Miluino/Miluino_MA1_hardware/docs/Техническая документация/02_Питание_и_внешние_выходы.md

# Питание платы и ограничение питания внешних устройств

## Источники и домены

Плата имеет два раздельных USB-C Device/UFP/Sink и вход VIN. От USB-C DAP постоянно формируется `+3V3_DAP` для STM32F103. Локальная target получает `+5V_TGT` от одного выбранного источника: коммутируемого VBUS USB-C DAP (`+5V_DAP_USB`), VBUS USB-C target (`USB_VBUS`) либо преобразованного VIN (`+5V_IN_Line`). От `+5V_TGT` отдельный TLV76133DCYR формирует `+3V3_TGT` для К1986. Общая GND не создаёт гальванической изоляции между доменами.

```text
USB-C DAP / USB_DAP_VBUS ─┬─ TLV76133DCYR ────────── +3V3_DAP
                          ├─ TPS2553-1 ────────────── +5V_DAP_OUT
                          │                 └─ Schottky + TLV76133DCYR ─ +3V3_DAP_OUT
                          └─ P-MOSFET ─ +5V_DAP_USB ───────┐
USB-C target / USB_VBUS ────────────────────────────────────┼─ T-селектор ─ +5V_TGT ─┬─ TLV76133DCYR ─ +3V3_TGT
VIN 8...18 В ─ LMR51410XDBVR ─ +5V_IN_Line ────────────────┘                        └─ TPS2553-1 ─ +5V_Out_Line
                                                                                                      └─ Schottky + TLV76133DCYR ─ +3V3_Out_Line
```

`+5V_Out_Line` и `+3V3_Out_Line` — имена защищённых электрических сетей ветви Output Power. Питание внешних устройств через Arduino и соответствующие контакты STMorpho берётся именно с этих сетей. `+5V_DAP_OUT` и `+3V3_DAP_OUT` образуют отдельную ветвь внешнего питания от USB-C DAP.

## Выбор питания локальной target

T-образный четырёхконтактный селектор имеет центральный контакт `+5V_TGT` и три внешних контакта источников. Один джампер соединяет только один источник с target; автоматического приоритета нет. Одновременно подключённые физические источники допустимы, поскольку невыбранные входы селектора разомкнуты. Без джампера силовое питание target отключено, тогда как домен DAP может оставаться под напряжением.

| Вход селектора | Путь | Особенность |
|---|---|---|
| DAP | `USB_DAP_VBUS` → P-MOSFET → `+5V_DAP_USB` | Ключ управляется STM32F103; ток target обходит TPS2553-1 внешних выходов DAP. |
| USB target | `USB_VBUS` USB-C target напрямую | Дополнительного eFuse либо ограничения тока VBUS на плате нет. |
| VIN | VIN → LMR51410XDBVR → `+5V_IN_Line` | Вход 8...18 В, номинально 12 В; защита от переполюсовки и длительного перенапряжения требуется от внешнего источника. |

VIN на Arduino и STMorpho относится к одной входной сети. Контакты +5V/+3V3 Arduino, выходы DAP и прямые контакты STMorpho не служат входами питания платы. BUcc К1986 соединён с `+3V3_TGT`; отдельного резервного источника нет.

### Преобразователь VIN

Выбран LMR51410XDBVR: синхронный понижающий преобразователь 400 кГц, PFM при малой нагрузке, номинальный ток микросхемы 1 А. В схеме предусмотрены входные 4,7 мкФ и 100 нФ X7R на 50 В, дроссель 33 мкГн с `Irms ≥ 1,5 А` и `Isat ≥ 2,5 А`, bootstrap 100 нФ X7R на 16 В, выходные 22 мкФ X7R на 16 В и делитель FB 118 кОм / 22,1 кОм с допуском 1 %. EN подключён непосредственно к VIN; отдельный UVLO-делитель не установлен. Встроенная аварийная защита преобразователя не задаёт допустимый ток внешней нагрузки.

### Стабилизаторы 3,3 В

Четыре ветви используют TLV76133DCYR: `+3V3_DAP`, `+3V3_TGT`, `+3V3_DAP_OUT` и `+3V3_Out_Line`. Для каждого LDO предусмотрены керамические X7R: 1 мкФ на входе и 4,7 мкФ на выходе; эффективную выходную ёмкость и тепловой режим необходимо подтвердить для выбранных компонентов и разводки. Внешние ветви 3,3 В питаются через отдельные последовательные диоды Шоттки. В схеме для DAP это VD101/VD102, для Output Power — VD1/VD2: первый диод каждой пары блокирует продолжительное обратное питание пятивольтового выхода, второй соединяет выход LDO с его входом в направлении отвода обратного тока. Конкретные диоды ещё не выбраны; эта схема не является идеальной безынерционной развязкой источников.

## Два независимых ограничителя тока

| Ветвь | Вход и выходы | Управление | Установка ограничения |
|---|---|---|---|
| Внешние выходы DAP | `USB_DAP_VBUS` → TPS2553-1 → `+5V_DAP_OUT` и LDO `+3V3_DAP_OUT` | `DAP_TARGET_PWR_EN` от PA1 STM32F103 | R122 = 100 кОм, 1 % |
| Output Power | `+5V_TGT` → TPS2553-1 → `+5V_Out_Line` и LDO `+3V3_Out_Line` | `TGT_OUTPUT_PWR_EN` от PB10 К1986 | R28 = 100 кОм, 1 % |

Каждый TPS2553-1 ограничивает общий входной ток **своей** пятивольтовой и трёхвольтовой нагрузок. Ток LDO 3,3 В берётся из той же защищённой ветви 5 В. При RILIM = 100 кОм типовой порог около 266 мА; расчётный разброс по формулам производителя с допуском резистора составляет ориентировочно 232...306 мА. Значение 300 мА не является гарантированным точным порогом отдельного ключа и не обеспечивается как суммарный аппаратный предел двух ключей. Диапазон и нагрев требуют измерений на прототипе.

У каждого ключа предусмотрены входной X7R 1 мкФ и выходной X7R 22 мкФ; эффективная выходная ёмкость при рабочем напряжении должна быть не менее 10 мкФ. Выходы двух ключей между собой не объединяются. Версия `-1` защёлкивает аварийное отключение: для восстановления требуется переключить соответствующий EN либо снять питание; автоматическое программное повторное включение не предусмотрено.

### Внешние выходы DAP

`+5V_DAP_OUT` и `+3V3_DAP_OUT` расположены отдельно от XP7 и имеют общий ограничитель тока. GND внешней платы берётся с соседнего `SPARE JMP`. Контакт XP7.1 `EXT_VTREF` остаётся входом фактического питания логики внешней target: 3,3 В необходимо вернуть на него даже при питании платы от одного из выходов DAP. При использовании выхода 5 В внешняя плата должна самостоятельно сформировать 3,3 В для своей логики.

PA1 STM32F103 формирует активный высоким уровнем `DAP_TARGET_PWR_EN`: он напрямую подан на EN первого TPS2553-1 и через R112 = 1 кОм управляет затвором NMOS 2N7002 в цепи силового P-MOSFET. Подтяжка затвора NMOS к GND 10 кОм и подтяжка затвора P-MOSFET к его истоку удерживают оба тракта выключенными после сброса. Прошивка разрешает их после USB `SET_CONFIGURATION` для конфигурации 500 мА и отключает при suspend, сбросе или деконфигурации USB и потере VBUS. `FAULT` этого TPS2553-1 подключён только к местной цепи светодиода, к микроконтроллерам он не подаётся.

TPS2553-1 имеет защиту от обратного напряжения с конечным временем отключения. Она блокирует продолжительную подпитку VBUS через внешний выход, но не заменяет мгновенный ideal-diode. Подавать на выходы питание от другого источника без специально рассчитанной развязки нельзя. Для 3,3-вольтового LDO возможны кратковременный заряд его входной ёмкости и токи утечки; допустимость конкретной внешней схемы подтверждается измерениями.

### Output Power для Arduino и STMorpho

PB10 К1986 (вывод 55) через штатно установленный R1004 = 0 Ом управляет сетью `TGT_OUTPUT_PWR_EN` и EN второго TPS2553-1 независимо от выбранного входа T-селектора. R27 = 10 кОм подтягивает EN к GND: при сбросе и до настройки PB10 выходы выключены. Включение выполняется только по явной команде прошивки. Альтернативный R1104 = 0 Ом к `PB10_Line`/CN10.2 штатно не установлен; одновременная установка R1004 и R1104 запрещена. `DAP_TARGET_PWR_EN` электрически не управляет этим ключом.

| Шина | Контакты Arduino | Защищённые контакты STMorpho |
|---|---|---|
| `+5V_Out_Line` | +5V | CN7.11, CN7.18 |
| `+3V3_Out_Line` | +3V3 | CN7.9, CN7.16 |

Нагрузки всех перечисленных контактов суммируются на входе второго TPS2553-1. Выходы разрешены только как источники питания внешних устройств; обратная подача напряжения запрещена. Номиналы светодиодов и их последовательных резисторов в цепях `FAULT` обеих ветвей пока не выбраны.

### Прямые контакты STMorpho для контроля питания

| Сеть | Контакты | Допустимое применение |
|---|---|---|
| `+3V3_TGT` | CN7.5, CN7.12 (IOREF), CN7.33 (BUcc) | Только высокоомное измерение напряжения. |
| `+5V_TGT` | CN7.6, CN7.26, CN10.8 | Только высокоомное измерение напряжения. |

Эти контакты находятся **до** второго TPS2553-1. Питать от них shield или иную внешнюю нагрузку и подавать на них напряжение нельзя: ключ не ограничит такой ток и не защитит от обратной подачи. IOREF показывает питание логики К1986 даже при выключенной ветви Output Power; CN7.26 позволяет контролировать `+5V_TGT` при её выключении.

## Индикация и контроль аварии

`FAULT` ключа Output Power имеет активный низкий уровень, подтянут R26 = 100 кОм к `+5V_TGT` и подключён к локальному индикатору. Этот же узел соединён с затвором VT1 = 2N7002; исток VT1 соединён с GND, сток подтянут R24 = 10 кОм к `+3V3_TGT`. Штатно не установленный R25 = 1 кОм может соединить сток с PE3 К1986 и STMorpho CN10.10. При установленном R25 **высокий уровень PE3 означает аварию**, низкий — отсутствие активного `FAULT`, но не доказывает наличие выходного напряжения. В такой комплектации CN10.10 нельзя независимо использовать шилдом. В базовой комплектации R25 = DNP и PE3 остаётся GPIO.

`FAULT` ключа внешних выходов DAP остаётся только на местном светодиоде; STM32F103 и К1986 его не считывают. Цвет, модели и токоограничивающие резисторы обоих индикаторов ожидают выбора конкретных светодиодов.

## Бюджет USB-C DAP и других источников

Для работы от USB-C DAP принят бюджет 500 мА: до 100 мА с запасом на STM32F103, до 100 мА с запасом на К1986 и **не более 300 мА суммарно** на все внешние нагрузки двух ветвей (`+5V_DAP_OUT`/`+3V3_DAP_OUT` и Output Power на Arduino/STMorpho). Это эксплуатационный бюджет, а не общий порог двух TPS2553-1. Ток нештатной нагрузки прямых контактов STMorpho также потреблял бы этот бюджет, не проходя через Output Power TPS2553-1.

При питании target от USB-C target потребление должно соответствовать разрешённому его USB-хостом току; конфигурация USB-C DAP на этот порт не распространяется. Для VIN допустимый ток определяют внешний источник, преобразователь, тепловой режим и проверка прототипа. Номинальный ток LMR51410XDBVR 1 А не является разрешением нагружать разъёмы платы на 1 А.

## USB-C и защита портов

Оба USB-C работают только как Device/UFP/Sink: CC1 и CC2 каждого разъёма имеют отдельные Rd 5,1 кОм, 1 % к GND. Высокие напряжения USB Power Delivery, Host/Source и обратная подача на VBUS не поддерживаются. Пары A6/B6 и A7/B7 розетки объединяются соответственно как D+ и D−. Экраны обоих разъёмов соединяются с GND напрямую.

На D+/D− каждого порта установлена отдельная малоёмкостная сборка USBLC6-2SC6 по проходной схеме; её VBUS подключён к VBUS соответствующего разъёма, GND — коротким соединением к общей земле. Рядом находятся локальные конденсаторы VBUS 100 нФ: C110 у DAP и C6 у target. Они развязывают VBUS и не меняют роль USBLC6-2SC6: сборка защищает сигнальные линии от ESD, но не ограничивает силовой ток. Последовательные резисторы USB D+/D− и CC-подтяжки остаются самостоятельными элементами.

## Сброс, полное отключение и ограничения

При изменении MODE К1986 требуется полный power cycle. Снятие джампера T-селектора разрывает штатные силовые пути target, но включённый DAP или внешний shield может частично подпитывать выключенный домен через сигнальные линии SWD/JTAG, VCP, MCO, USB или GPIO. Перед отключением target необходимо исключить активные сигналы в выключенный домен; для DAP доступны `DAP_ROUTE=OFF`, отключение VCP и снятие R1003 линии MCO. Постоянный разрядный резистор `+3V3_TGT` установлен, его окончательный номинал и время разряда проверяются на прототипе. Индикатор питания target не заменяет измерение остаточного напряжения.

Открыты для проверки на прототипе: фактические пороги двух TPS2553-1, ёмкости конденсаторов при рабочем смещении, нагрев LDO и преобразователя, обратные токи через выходы, время разряда `+3V3_TGT`, работа при одновременном подключении двух USB-хостов и конкретные типы диодов, MOSFET и индикаторов.

См. также [общее описание](01_Общее_описание_платы.md), [распиновку К1986](03_К1986_распиновка_и_программирование.md) и [распиновку DAP](04_Программатор_распиновка.md).
