Miluino/Miluino_MA1_hardware/docs/Техническая документация/03_К1986_распиновка_и_программирование.md

# К1986ВЕ92FI: распиновка, переключатели и программирование

## Электрические условия

К1986ВЕ92FI питается от `+3V3_TGT`, сформированной из выбранной T-селектором шины `+5V_TGT`. BUcc подключён к тому же домену; независимого резервного питания нет. Логические уровни Arduino, STMorpho и интерфейсов отладки рассчитаны на 3,3 В. Силовые контакты +5V/+3V3 Arduino получают питание от включаемой отдельно ветви Output Power; IOREF всегда показывает `+3V3_TGT`. Контакты Morpho, соединённые с `+5V_TGT` и `+3V3_TGT` напрямую, предназначены только для высокоомного контроля напряжения: перечень и ограничения приведены в [документе по питанию](02_Питание_и_внешние_выходы.md).

## Все выводы К1986ВЕ92FI

В таблице указан физический номер вывода корпуса и его связь с разъёмами при штатной комплектации. Для переключаемых цепей приведены оба функциональных варианта; DNP-ветвь проводит сигнал только после установки соответствующего резистора.

| № | Вывод К1986 | Arduino | STMorpho / внешний узел | Назначение |
|---:|---|---|---|---|
| 1 | Ucc | IOREF показывает эту шину; контакт Arduino +3V3 питается отдельно | Шина `+3V3_TGT`; CN7.5/CN7.12 | Основное цифровое питание, обязательна локальная развязка |
| 2 | PF0 | D11/MOSI через `SEL_D11_SPI_PWM` | CN7.1 RAW; CN10.15 через D11_SEL | SSP1_TXD; в MODE=110 используется UART2-загрузчиком |
| 3 | PF1 | D13/SCK | CN10.11 | SSP1_CLK; локальный LED не подключается; в MODE=110 используется UART2-загрузчиком |
| 4 | PF2 | D10/CS через `SEL_D10_SPI_PWM` | CN10.18 RAW; CN10.17 через D10_SEL | SSP1_FSS; не объединять напрямую с PA2 |
| 5 | PF3 | D12/MISO | CN10.13 | SSP1_RXD, прямое соединение |
| 6 | PF4/MODE0 | - | Только локальный конфигуратор MODE0 | Бит MODE0; намеренно не соединяется с CN7.7/BOOT0, Morpho и внешними разъёмами |
| 7 | PF5/MODE1 | - | Только локальный конфигуратор MODE1 | Бит MODE1; намеренно не выводится на Morpho и внешние разъёмы |
| 8 | PF6/MODE2 | - | Только локальный конфигуратор MODE2 | Бит MODE2; намеренно не выводится на Morpho и внешние разъёмы |
| 9 | DP | - | CN10.12; USB-C целевого МК | USB D+; позиция соответствует PA12/USB_DP NUCLEO-F103RB; не объединять с USB встроенного отладчика |
| 10 | DN | - | CN10.14; USB-C целевого МК | USB D-; позиция соответствует PA11/USB_DM NUCLEO-F103RB; требуется ESD-защита и обвязка по datasheet |
| 11 | GND | GND | Общая GND; контакты GND Morpho | Цифровая земля |
| 12 | Ucc | IOREF показывает эту шину; контакт Arduino +3V3 питается отдельно | Шина `+3V3_TGT`; CN7.5/CN7.12 | Основное цифровое питание, обязательна локальная развязка |
| 13 | BUcc | — | CN7.33 | BUcc напрямую питается от основной целевой шины `+3V3_TGT`; отдельный резервный источник не предусмотрен. CN7.33 допускается только для высокоомного контроля напряжения, без питания шилда и внешней подачи напряжения |
| 14 | STANDBY | - | CN7.4 через R11 (`R_STANDBY_SER`) | Выходной флаг режима Standby; без подтяжки, shield использует линию только как вход |
| 15 | PE7/OSC32_OUT | - | CN7.27 | LSE-кварц либо GPIO через взаимоисключающие мосты; позиция соответствует PC15/OSC32_OUT F103RB |
| 16 | PE6/OSC32_IN | - | CN7.25 | LSE-кварц либо GPIO через взаимоисключающие мосты; позиция соответствует PC14/OSC32_IN F103RB |
| 17 | WAKEUP | - | CN7.3 через нормально не установленный `R_WAKEUP_EN`; R12 (`R_WAKEUP_PULL`) к VCC установлен, номинал уточняется | Активный низким уровнем вход пробуждения из Standby; внешний источник только open-drain/open-collector, 3,3 В |
| 18 | RESET | RESET | CN7.14 | `TARGET_nRESET` с единственной подтяжкой к `+3V3_TGT` и C1=100 нФ к GND; все внешние источники только open-drain/open-collector |
| 19 | OSC_IN | - | DAP_MCO через R109 и R1003 default; X_HSE через R1103; CN7.29 через R1203 | Штатный вход 8 МГц от DAP; для MCO/внешнего генератора требуется HSEBYP=1, для локального кварца HSEBYP=0 |
| 20 | OSC_OUT | - | X_HSE через R1213; CN7.31 через R1113; к DAP не подключать | Выход аналогового усилителя HSE в режиме кварца; в режиме DAP_MCO должен оставаться ненагруженным |
| 21 | PE3 | - | CN10.10; сток VT1 через штатно не установленный R25=1 кОм | Свободный GPIO при DNP R25; после установки R25 — вход аварии ветви Output Power, высокий уровень означает срабатывание `FAULT`; shield не должен управлять CN10.10 |
| 22 | PE2 | D3/PWM | CN10.31 | TMR2_CH3; аппаратный PWM |
| 23 | AGND1 | - | Общая аналоговая земля; CN10.32 | Отдельный физический вывод, на Morpho доступен через общую сеть AGND |
| 24 | AUcc1 | - | Общая аналоговая шина; на CN10.7 не выведена | Отдельный физический вывод аналогового питания; CN10.7 подключён к `AREF_Line` |
| 25 | PE1 | - | CN7.37 | Свободный GPIO; также DAC2_REF и альтернативные CAN/таймерные функции |
| 26 | PE0/DAC2_OUT | A0 в положении DAC `SEL_A0_ADC_DAC` | CN10.6 RAW; CN7.28 через A0_SEL | Выход ЦАП; нельзя объединять напрямую с PD2 |
| 27 | AGND | - | CN10.32 | Основная аналоговая земля; постоянно соединяется с общей GND с учётом требований к разводке |
| 28 | AUcc | — | - | Аналоговое питание и внутренняя опора АЦП; на CN10.7 выведена отдельная сеть `AREF_Line`, штатно связанная с `+3V3_TGT` через R1009 |
| 29 | PD7/ADC7 | A5 в положении ADC | CN10.28 RAW; CN7.38 через A5_SEL | Освобождается, если A5 переключён на I2C/SCL |
| 30 | PD4/ADC4/JB_TDO | A2 | CN7.32 | Недоступен как ADC во время отладки через JTAG_B |
| 31 | PD0/ADC0_REF+/UART2_RXD/JB_TMS | - | CN10.34/JTAG_B через R1005; DAP_VCP_TX через R1105; R1109 соединяет AREF с `PD0/JB_TMS_Line` и штатно не установлен | Будущая внешняя опора: R1109+R1005 установлены, CN10.34 не используется, JTAG_B отключён |
| 32 | PD1/ADC1_REF-/UART2_TXD/JB_TCK | - | CN10.36/JTAG_B через R1006; DAP_VCP_RX через R1106; R1206=0 Ом (DNP) к GND со стороны МК | Для будущей внешней опоры R1006/R1106 сняты, R1206 установлен; штатно доступен RAW/VCP по установленному каналу |
| 33 | PD2/ADC2/JB_TRST | A0 в положении ADC `SEL_A0_ADC_DAC` | CN10.4 RAW; CN7.28 через A0_SEL | Штатный аналоговый вход A0; конфликт с JTAG_B |
| 34 | PD3/ADC3/JB_TDI | A1 | CN7.30 | Прямой аналоговый вход; конфликт с JTAG_B |
| 35 | PD5/ADC5 | A3 | CN7.34 | Прямой аналоговый вход; JTAG_B его не занимает |
| 36 | PD6/ADC6 | A4 в положении ADC | CN10.26 RAW; CN7.36 через A4_SEL | Освобождается, если A4 переключён на I2C/SDA |
| 37 | NC | - | Не подключать | Корпусной вывод без электрического подключения |
| 38 | Ucc | IOREF показывает эту шину; контакт Arduino +3V3 питается отдельно | Шина `+3V3_TGT`; CN7.5/CN7.12 | Основное цифровое питание, обязательна локальная развязка |
| 39 | GND | GND | Общая GND; контакты GND Morpho | Цифровая земля |
| 40 | PC2 | - | CN7.35 | Свободный GPIO |
| 41 | PC1/SDA1 | D18/SDA; A4 в положении I2C | CN10.5; CN10.38 RAW; CN7.36 через A4_SEL | В режиме I2C A4 и D18 являются одной сетью SDA |
| 42 | PC0/SCL1 | D19/SCL; A5 в положении I2C | CN10.3; CN10.30 RAW; CN7.38 через A5_SEL | В режиме I2C A5 и D19 являются одной сетью SCL |
| 43 | PB0/JA_TDO | - | CN7.21 | JTAG_A TDO; у F103RB совмещён с D3 на CN10.31, но здесь выведен отдельно |
| 44 | PB1/JA_TMS | - | CN7.13 | JTAG_A TMS; GPIO доступен только после отключения JTAG_A |
| 45 | PB2/JA_TCK | - | CN7.15 | JTAG_A TCK; GPIO доступен только после отключения JTAG_A |
| 46 | PB3/JA_TDI | - | CN7.17 | JTAG_A TDI; позиция соответствует PA15/JTDI NUCLEO-F103RB |
| 47 | PB4/JA_TRST | - | CN7.23 | JTAG_A TRST; у F103RB совмещён с D5 на CN10.27, но здесь выведен отдельно |
| 48 | Ucc | IOREF показывает эту шину; контакт Arduino +3V3 питается отдельно | Шина `+3V3_TGT`; CN7.5/CN7.12 | Основное цифровое питание, обязательна локальная развязка |
| 49 | GND | GND | Общая GND; контакты GND Morpho | Цифровая земля |
| 50 | PB5/UART1_TXD | D1/TX | CN10.35 | Постоянное соединение с Arduino D1; VCP использует UART2 на PD0/PD1 |
| 51 | PB6/UART1_RXD | D0/RX | CN10.37 | Постоянное соединение с Arduino D0; VCP использует UART2 на PD0/PD1 |
| 52 | PB7 | D8 | CN10.21 | Прямое соединение; свободны альтернативные таймерные функции |
| 53 | PB8 | D7 | CN10.23 | Прямое соединение; также TMR3_CH4N/COMP_OUT |
| 54 | PB9 | USER_BUTTON через `R_BUTTON_EN` | CN10.1 | GPIO/EXT_INT4; снятие `R_BUTTON_EN` отключает кнопку и её подтяжку от линии |
| 55 | PB10 | - | `TGT_OUTPUT_PWR_EN` через штатный R1004=0 Ом; CN10.2 через неустановленный R1104=0 Ом | Управление `EN` второго TPS2553-1; R27=10 кОм к GND удерживает выходы выключенными до явной команды прошивки, автоматического включения после инициализации нет |
| 56 | PA7/CAN1_RX | D5 в положении CAN | CN10.24 RAW; CN10.27 через D5_SEL | Не объединять напрямую с PA5; используется для совместимости CAN UNO R4 |
| 57 | PA6/CAN1_TX | D4/CANTX | CN10.29 | GPIO и CAN1_TX выбираются внутренним мультиплексором МК |
| 58 | PA5/TMR1_CH3 | D5 в положении PWM; LED4 через R18 (`R_LED4`) | CN10.22 RAW; CN10.27 через D5_SEL | Аппаратный PWM; установленный LED нагружает D5 при использовании линии как вход |
| 59 | PA4/TMR1_CH2N | D6/PWM | CN10.25 | Прямое соединение; аппаратный PWM |
| 60 | PA3/TMR1_CH2 | D9/PWM; LED3 через R17 (`R_LED3`) | CN10.19 | Аппаратный PWM; установленный LED нагружает D9 при использовании линии как вход |
| 61 | PA2/TMR1_CH1N | D10 в положении PWM; LED2 через R16 (`R_LED2`) | CN10.16 RAW; CN10.17 через D10_SEL | Альтернатива PF2/CS; LED не нагружает D10 в штатном SPI-положении селектора |
| 62 | PA1/TMR1_CH1 | D11 в положении PWM; LED1 через R15 (`R_LED1`) | CN7.2 RAW; CN10.15 через D11_SEL | Альтернатива PF0/MOSI; LED не нагружает D11 в штатном SPI-положении селектора |
| 63 | PA0/EXT_INT1 | D2 | CN10.33 | Прямое соединение; пользовательская кнопка перенесена на PB9 и не нагружает D2 |
| 64 | GND | GND | Общая GND; контакты GND Morpho | Цифровая земля |

## Контакты Arduino

| Контакт | Подключение к К1986 и штатная функция | Альтернативная комплектация или ограничение |
|---|---|---|
| NC/BOOT | Не подключён | MODE[2:0] находится только на локальных конфигураторах. |
| IOREF | `+3V3_TGT` | Опорный уровень shield 3,3 В, не защищённый выход нагрузки. |
| RESET | `TARGET_nRESET` | Только низкий уровень по open-drain/open-collector. |
| +3V3 | `+3V3_Out_Line` | Защищённый выход Output Power, не вход. |
| +5V | `+5V_Out_Line` | Защищённый выход Output Power, не вход. |
| GND | Общая GND | — |
| VIN | Вход преобразователя LMR51410XDBVR | 8...18 В, номинально 12 В. |
| AREF | Через R1009 к `+3V3_TGT` | Внешняя опора в базовой комплектации запрещена; см. раздел «AREF». |
| A0 | Через R1000 к PD2/ADC2 | R1100 вместо R1000 переключает A0 на PE0/DAC2_OUT. |
| A1 | PD3/ADC3 | Аналоговый вход; функция OPAMP+ UNO R4 не воспроизводится. |
| A2 | PD4/ADC4 | Аналоговый вход; функция OPAMP− UNO R4 не воспроизводится. |
| A3 | PD5/ADC5 | Аналоговый вход; функция OPAMP_OUT UNO R4 не воспроизводится. |
| A4 | Через R1002 к PD6/ADC6 | R1102 вместо R1002 подключает PC1/SDA1 и дублирует D18. |
| A5 | Через R1001 к PD7/ADC7 | R1101 вместо R1001 подключает PC0/SCL1 и дублирует D19. |
| D19/SCL | PC0/SCL1 | Постоянный I²C SCL; A5 может дублировать его. |
| D18/SDA | PC1/SDA1 | Постоянный I²C SDA; A4 может дублировать его. |
| D13/SCK | PF1/SSP1_CLK | Локальный светодиод к D13 не подключён; в MODE=110 линия занята UART2-загрузчиком. |
| D12/MISO | PF3/SSP1_RXD | Постоянное соединение. |
| D11/MOSI/PWM | Через R1010 к PF0/SSP1_TXD | R1110 вместо R1010 подключает PA1/TMR1_CH1 для PWM. |
| D10/CS/PWM | Через R1011 к PF2/SSP1_FSS | R1111 вместо R1011 подключает PA2/TMR1_CH1N для PWM. |
| D9/PWM | PA3/TMR1_CH2 | Локальный LED3 может нагружать входной режим. |
| D8 | PB7 | GPIO. |
| D7 | PB8 | GPIO и альтернативные функции таймера/компаратора. |
| D6/PWM | PA4/TMR1_CH2N | Постоянное соединение. |
| D5/PWM/CANRX | Через R1012 к PA5/TMR1_CH3 | R1112 вместо R1012 подключает PA7/CAN1_RX. |
| D4/CANTX | PA6/CAN1_TX | Физическая шина CAN требует внешнего трансивера. |
| D3/PWM | PE2/TMR2_CH3 | Постоянное соединение. |
| D2 | PA0/EXT_INT1 | Пользовательская кнопка находится на PB9 и не нагружает D2. |
| D1/TX | PB5/UART1_TXD | Не переключается на VCP. |
| D0/RX | PB6/UART1_RXD | Не переключается на VCP. |

При штатном `MODE=001` аналоговые PD2–PD7 свободны от JTAG_B. При `MODE=000` JTAG_B занимает PD0–PD4, поэтому A0–A2 во время отладки недоступны. На аналоговые входы PD2–PD7 нельзя подавать 5 В; для I²C на A4/A5 подтяжки допускаются только к 3,3 В. Установленные пользовательские LED на PA3 и PA5 создают нагрузку при использовании D9/D5 как входов.

## STMorpho CN7 и CN10

Расположение контактов соответствует механической карте NUCLEO-F103RB, но электрические назначения определены схемой Miluino. `RAW` означает доступ к выводу К1986 без функционального выбора Arduino; исключения PD0/PD1 и PE6/PE7 указаны в таблицах. Повторяющиеся контакты одной сети не являются независимыми GPIO.

### CN7

| № | Цепь Miluino | Соединение / комплектация | Функция и ограничение |
|---:|---|---|---|
| 1 | PF0_RAW(2) | Прямо к выводу МК; без SB на ветви Morpho | RAW-доступ к PF0; SSP1_TXD/MOSI и линия UART2-загрузчика в MODE=110 |
| 2 | PA1_RAW(62) | Прямо к выводу МК; без SB на ветви Morpho | RAW-доступ к PA1/TMR1_CH1; альтернативный источник PWM для D11 |
| 3 | WAKEUP(17) | Через нормально не установленный резистор 0 Ом `R_WAKEUP_EN`; на стороне МК постоянная подтяжка R12 (ориентир 50...100 кОм) к VCC | Активный низким уровнем вход пробуждения из Standby; shield управляет только open-drain/open-collector, не является RESET |
| 4 | STANDBY(14) | Через установленный последовательный резистор R11 (ориентир 1 кОм) без подтяжки | Выходной флаг режима Standby; shield должен воспринимать линию только как вход |
| 5 | +3V3_TGT | Прямо к питанию К1986; второй TPS2553-1 этот контакт не ограничивает | Только высокоомный контроль напряжения target; питание шилда и внешняя подача напряжения строго запрещены |
| 6 | +5V_TGT | Прямо к выходу T-селектора; у Miluino не является внешним входом E5V Nucleo | Только высокоомный контроль напряжения target; питание шилда и внешняя подача напряжения строго запрещены |
| 7 | NC | Не устанавливать SB к MODE0 или другим сигналам | Позиция BOOT0 Nucleo намеренно оставлена неподключённой |
| 8 | GND | Прямо к общей GND | Общий провод |
| 9 | +3V3_Out_Line | Прямо к защищённой шине после второго TPS2553-1 и отдельного LDO | Дополнительный выход 3,3 В для шилда; общий токовый предел с Arduino +3V3/+5V и CN7.11/16/18 |
| 10 | NC | Не подключать | Сохранён штатный NC Nucleo |
| 11 | +5V_Out_Line | Прямо к защищённой шине после второго TPS2553-1 | Дополнительный выход 5 В для шилда; общий токовый предел с Arduino +3V3/+5V и CN7.9/16/18 |
| 12 | +3V3_TGT | Прямо к питанию К1986; показывает уровень логики и при выключенном втором TPS2553-1 | Только опорное напряжение для шилда; использовать как источник питания или подавать на него внешнее напряжение строго запрещено |
| 13 | PB1/JA_TMS(44) | Прямо к CN7 и входу A группового `JTAG_Channel_Selector` | JTAG_A TMS/SWDIO и GPIO после освобождения отладочного порта |
| 14 | RESET(18) | Общая сеть `TARGET_nRESET` с подтяжкой к `+3V3_TGT`; кнопка, DAP, внешний программатор и shield могут только притягивать её к GND | Аппаратный сброс К1986 и подключённого shield; активный высокий уровень, подтяжка к 5 В и внешний конденсатор без проверки запрещены |
| 15 | PB2/JA_TCK(45) | Прямо к CN7 и входу A группового `JTAG_Channel_Selector` | JTAG_A TCK/SWCLK и GPIO после освобождения отладочного порта |
| 16 | +3V3_Out_Line | Выход отдельного LDO после второго TPS2553-1; общая защищённая ветвь с Arduino +3V3 | Выход питания 3,3 В, отключаемый PB10; нагрузка входит в общий предел ключа |
| 17 | PB3/JA_TDI(46) | Прямо к CN7 и входу A группового `JTAG_Channel_Selector` | JTAG_A TDI и GPIO после освобождения отладочного порта |
| 18 | +5V_Out_Line | Выход второго TPS2553-1; общая защищённая ветвь с Arduino +5V | Выход питания 5 В, отключаемый PB10; нагрузка входит в общий предел ключа |
| 19 | GND | Прямо к общей GND | Общий провод |
| 20 | GND | Прямо к общей GND | Общий провод |
| 21 | PB0/JA_TDO(43) | Прямо к CN7 и входу A группового `JTAG_Channel_Selector` | JTAG_A TDO и GPIO после освобождения отладочного порта |
| 22 | GND | Прямо к общей GND | Общий провод |
| 23 | PB4/JA_TRST(47) | Прямо к CN7 и входу A группового `JTAG_Channel_Selector` | JTAG_A nTRST и GPIO после освобождения отладочного порта |
| 24 | VIN | Прямо к общей входной сети VIN Arduino/STMorpho, далее на `LMR51410XDBVR`, формирующий `+5V_IN_Line` перед T-селектором | Внешний вход питания платы 8...18 В, номинально 12 В; отдельной входной защиты на плате нет |
| 25 | PE6/OSC32_IN(16) | Через установленный R1007; альтернативный неустановленный R1107 подключает локальный кварц LSE | Вход LSE либо GPIO PE6 при отключённом кварце |
| 26 | +5V_TGT | Прямо к выходу T-селектора, до второго TPS2553-1 | Только высокоомный контроль питания target при отключённых защищённых выходах; питание шилда и внешняя подача напряжения строго запрещены |
| 27 | PE7/OSC32_OUT(15) | Через установленный R1008; альтернативный неустановленный R1108 подключает локальный кварц LSE | Выход LSE либо GPIO PE7 при отключённом кварце |
| 28 | A0_SEL | Общий контакт `SEL_A0_ADC_DAC`; варианты PD2/ADC2 и PE0/DAC2_OUT соединяются селектором 1-of-2 либо парой взаимоисключающих SB | Arduino A0: аналоговый вход или выход ЦАП |
| 29 | OSC_IN(19) | Через нормально не установленный R1203; для внешнего генератора снять R1003 и установить R1203 | Вход HSE от штатного DAP_MCO, локального кварца или внешнего генератора |
| 30 | A1=PD3/ADC3(34) | Прямо к PD3; без SB | Arduino A1, аналоговый вход ADC3 |
| 31 | OSC_OUT(20) | Через нормально не установленный R1113; в штатном режиме DAP_MCO оставить отключённым | Выход аналогового усилителя HSE только в режиме локального кварца |
| 32 | A2=PD4/ADC4(30) | Прямо к PD4; без SB | Arduino A2, аналоговый вход ADC4; конфликтует с JTAG_B TDO |
| 33 | BUcc(13), +3V3_TGT | BUcc К1986 напрямую питается от целевой шины; отдельного резервного источника нет | Только высокоомный контроль напряжения; питание шилда и внешняя подача напряжения через контакт строго запрещены |
| 34 | A3=PD5/ADC5(35) | Прямо к PD5; без SB | Arduino A3, аналоговый вход ADC5 |
| 35 | PC2(40) | Прямо к выводу МК; без SB | Дополнительный GPIO PC2 |
| 36 | A4_SEL | Общий контакт `SEL_A4_ADC_I2C`; PD6/ADC6 и PC1/SDA1 подключаются механическим селектором либо взаимоисключающими `SB_A4_ADC`/`SB_A4_I2C` | Arduino A4: ADC6 либо дубликат I2C SDA/D18 |
| 37 | PE1(25) | Прямо к выводу МК; без SB | Дополнительный GPIO; доступны DAC2_REF и альтернативные CAN/таймерные функции |
| 38 | A5_SEL | Общий контакт `SEL_A5_ADC_I2C`; PD7/ADC7 и PC0/SCL1 подключаются механическим селектором либо взаимоисключающими `SB_A5_ADC`/`SB_A5_I2C` | Arduino A5: ADC7 либо дубликат I2C SCL/D19 |

### CN10

| № | Цепь Miluino | Соединение / комплектация | Функция и ограничение |
|---:|---|---|---|
| 1 | PB9(54) | Прямо к выводу МК; без SB | Дополнительный GPIO PB9 |
| 2 | PB10_Line через штатно не установленный R1104 от PB10(55) | R1104 соединяет контакт Morpho с PB10 только в альтернативной сборке; вместе с R1004 не устанавливать | PB10 штатно управляет выходами питания Arduino через R1004 |
| 3 | D19=PC0/SCL1(42) | Прямо к PC0; без SB | Arduino D19 и основная аппаратная линия I2C SCL |
| 4 | PD2_RAW(33) | Прямо к PD2; без SB на ветви RAW | RAW-доступ к ADC2/JTAG_B nTRST; источник A0 в положении ADC |
| 5 | D18=PC1/SDA1(41) | Прямо к PC1; без SB | Arduino D18 и основная аппаратная линия I2C SDA |
| 6 | PE0_RAW(26) | Прямо к PE0; без SB на ветви RAW | RAW-доступ к DAC2_OUT; источник A0 в положении DAC |
| 7 | AREF_Line | Общая сеть с Arduino AREF; штатно через R1009 подключена к `+3V3_TGT`, к AUcc напрямую не подключена | Контакт AREF; внешнее напряжение при установленном R1009 запрещено |
| 8 | +5V_TGT | Прямо к выходу T-селектора; у Miluino не является отдельным входом USB-питания | Только высокоомный контроль напряжения target; питание шилда и внешняя подача напряжения строго запрещены |
| 9 | GND | Прямо к общей GND | Общий провод |
| 10 | PE3(21) | Прямо к PE3; R25=1 кОм (DNP) опционально подключает к нему сток VT1 | GPIO в позиции NC Nucleo; при установленном R25 — вход аварии ветви Output Power, внешний shield не должен управлять линией |
| 11 | D13=PF1/SSP1_CLK(3) | Прямо к D13; без локального LED и дополнительной нагрузки | Arduino D13 и SPI SCK |
| 12 | USB_DP(9) | Прямо к DP; USB-разъём и защиту подключать по отдельной согласованной USB-ветви | USB D+ целевого К1986 |
| 13 | D12=PF3/SSP1_RXD(5) | Прямо к PF3; без SB | Arduino D12 и SPI MISO/CIPO |
| 14 | USB_DN(10) | Прямо к DN; USB-разъём и защиту подключать по отдельной согласованной USB-ветви | USB D- целевого К1986 |
| 15 | D11_SEL | Общий контакт `SEL_D11_SPI_PWM`; PF0/MOSI и PA1/PWM соединяются селектором 1-of-2 либо взаимоисключающими `SB_D11_SPI`/`SB_D11_PWM` | Arduino D11: SPI MOSI/COPI либо аппаратный PWM |
| 16 | PA2_RAW(61) | Прямо к PA2; без SB на ветви RAW | RAW-доступ к PA2/TMR1_CH1N; источник PWM для D10 |
| 17 | D10_SEL | Общий контакт `SEL_D10_SPI_PWM`; PF2/CS и PA2/PWM соединяются селектором 1-of-2 либо взаимоисключающими `SB_D10_SPI`/`SB_D10_PWM` | Arduino D10: SPI CS/FSS либо аппаратный PWM |
| 18 | PF2_RAW(4) | Прямо к PF2; без SB на ветви RAW | RAW-доступ к SSP1_FSS; источник SPI CS для D10 |
| 19 | D9=PA3/TMR1_CH2(60) | Прямо к PA3; без SB | Arduino D9 с аппаратным PWM |
| 20 | GND | Прямо к общей GND | Общий провод |
| 21 | D8=PB7(52) | Прямо к PB7; без SB | Arduino D8, GPIO |
| 22 | PA5_RAW(58) | Прямо к PA5; без SB на ветви RAW | RAW-доступ к PA5/TMR1_CH3; источник PWM для D5 |
| 23 | D7=PB8(53) | Прямо к PB8; без SB | Arduino D7, GPIO; доступны TMR3_CH4N/COMP_OUT |
| 24 | PA7_RAW(56) | Прямо к PA7; без SB на ветви RAW | RAW-доступ к CAN1_RX; источник CANRX для D5 |
| 25 | D6=PA4/TMR1_CH2N(59) | Прямо к PA4; без SB | Arduino D6 с аппаратным PWM |
| 26 | PD6_RAW(36) | Прямо к PD6; без SB на ветви RAW | RAW-доступ к ADC6; источник A4 в положении ADC |
| 27 | D5_SEL | Общий контакт `SEL_D5_PWM_CAN`; PA5/PWM и PA7/CAN_RX соединяются селектором 1-of-2 либо взаимоисключающими `SB_D5_PWM`/`SB_D5_CAN` | Arduino D5: аппаратный PWM либо CANRX |
| 28 | PD7_RAW(29) | Прямо к PD7; без SB на ветви RAW | RAW-доступ к ADC7; источник A5 в положении ADC |
| 29 | D4=PA6/CAN1_TX(57) | Прямо к PA6; без SB | Arduino D4, GPIO или CAN1_TX через внутренний мультиплексор МК |
| 30 | PC0_RAW(42) | Прямо к PC0; без SB | RAW-дубликат сети D19/SCL1; не является независимой линией |
| 31 | D3=PE2/TMR2_CH3(22) | Прямо к PE2; без SB | Arduino D3 с аппаратным PWM |
| 32 | AGND | Прямо к AGND; AGND постоянно соединяется с общей GND согласно требованиям К1986 | Аналоговая земля платы |
| 33 | D2=PA0/EXT_INT1(63) | Прямо к PA0; без SB | Arduino D2, GPIO и вход внешнего прерывания |
| 34 | PD0/AREF/UART2_RX_RAW(31) | Через нормально установленный R1005; альтернативный R1105 подключает `DAP_VCP_TX` к PD0; R1109 подключает Arduino AREF к `PD0/JB_TMS_Line` только в режиме внешней опоры | RAW-доступ к ADC0/ADC0_REF+ и UART2_RXD; конфликтует с VCP, JTAG_B и UART-загрузчиком MODE=101 |
| 35 | D1=PB5/UART1_TXD(50) | Постоянно подключён к PB5; без выбора shield/VCP | Arduino D1/TX и передача UART1; VCP использует отдельный UART2 |
| 36 | PD1/REF-/UART2_TX_RAW(32) | Через нормально установленный R1006; альтернативный R1106 подключает PD1 к `DAP_VCP_RX`; R1206=0 Ом (DNP) при установке подключит PD1 к GND со стороны МК | RAW-доступ к ADC1/ADC1_REF- и UART2_TXD; внешний режим опоры требует альтернативной комплектации и проверки |
| 37 | D0=PB6/UART1_RXD(51) | Постоянно подключён к PB6; без выбора shield/VCP | Arduino D0/RX и приём UART1; VCP использует отдельный UART2 |
| 38 | PC1_RAW(41) | Прямо к PC1; без SB | RAW-дубликат сети D18/SDA1; не является независимой линией |

CN7.9/CN7.16 (+3,3 В) и CN7.11/CN7.18 (+5 В) относятся к защищённой ветви Output Power. CN7.5/CN7.12/CN7.33 (`+3V3_TGT`) и CN7.6/CN7.26/CN10.8 (`+5V_TGT`) подключены напрямую и допустимы только для высокоомного контроля напряжения. CN10.10 соединён с PE3: установка DNP-резистора R25 превращает его в вход аварии Output Power и исключает независимое управление контактом со стороны shield.

## Выбор функций резисторами 0 Ом

В группе с одинаковыми двумя последними цифрами `R10xx` — штатно установленная ветвь, `R11xx` и `R12xx` — штатно не установленные альтернативы. В каждой группе разрешена только одна установленная ветвь; перепайка выполняется при снятом питании. Джамперный выбор JTAG_A/B в эту систему не входит.

| Узел | Штатно установлен | Альтернатива DNP | Дополнительная альтернатива DNP |
|---|---|---|---|
| A0 ADC/DAC | R1000: PD2/ADC2 | R1100: PE0/DAC2_OUT | — |
| A5 ADC/I²C | R1001: PD7/ADC7 | R1101: PC0/SCL1 | — |
| A4 ADC/I²C | R1002: PD6/ADC6 | R1102: PC1/SDA1 | — |
| HSE OSC_IN | R1003: `DAP_MCO_Line` | R1103: локальный кварц | R1203: внешний генератор с CN7.29 |
| PB10 | R1004: `TGT_OUTPUT_PWR_EN` | R1104: `PB10_Line`/CN10.2 | — |
| PD0 UART2/JTAG_B | R1005: CN10.34 и JTAG_B | R1105: `DAP_VCP_TX` | — |
| PD1 UART2/JTAG_B | R1006: CN10.36 и JTAG_B | R1106: `DAP_VCP_RX` | R1206: PD1/ADC1_REF− к GND для внешней AREF |
| PE6 LSE/GPIO | R1007: CN7.25 | R1107: кварц LSE | — |
| PE7 LSE/GPIO | R1008: CN7.27 | R1108: кварц LSE | — |
| Arduino AREF | R1009: `+3V3_TGT` | R1109: `PD0/JB_TMS_Line` | — |
| D11 SPI/PWM | R1010: PF0/SSP1_TXD | R1110: PA1/TMR1_CH1 | — |
| D10 SPI/PWM | R1011: PF2/SSP1_FSS | R1111: PA2/TMR1_CH1N | — |
| D5 PWM/CANRX | R1012: PA5/TMR1_CH3 | R1112: PA7/CAN1_RX | — |

Для OSC_OUT пара R1113/R1213 не имеет штатно установленного канала: R1113 (DNP) выводит OSC_OUT на CN7.31, R1213 (DNP) соединяет его с локальным HSE-кварцем. Одновременно их устанавливать нельзя; R1013 не используется. Отдельные элементы: R9 = 0 Ом штатно подключает к PB9 кнопку и её подтяжку; R13 = 0 Ом (DNP) опционально соединяет WAKEUP с CN7.3. R25 = 1 кОм (DNP) подключает к PE3/CN10.10 инвертированный сигнал аварии Output Power и не является частью группы 0 Ом.

### AREF и аналоговая опора

В базовой комплектации R1009 соединяет AREF с `+3V3_TGT`; R1109 и R1206 не установлены. Подавать на AREF внешнее напряжение при R1009 запрещено. Альтернативная внешняя опора предусмотрена, но её точность и допустимый диапазон требуют проверки: снять R1009, R1006, R1105 и R1106; оставить R1005; установить R1109 и R1206; отключить JTAG_B и оставить CN10.34 без внешнего управления. Тогда AREF через R1109/R1005 идёт к PD0/ADC0_REF+, а PD1/ADC1_REF− через R1206 соединён с GND. В этом варианте PD0/PD1 не используются для VCP, JTAG_B или UART-загрузчика MODE=101.

## Программирование и отладка К1986

Три локальных конфигуратора задают PF4/MODE0, PF5/MODE1 и PF6/MODE2. Эти сигналы не соединены с Arduino BOOT, STMorpho или DBG_PORT_SEL. Положение MODE применяется после полного power cycle питания `+3V3_TGT`.

| MODE[2:0] | Запуск и порт | Основная конфигурация |
|---|---|---|
| 001 | Внутренняя Flash, JTAG_A на PB0–PB4 | Штатная отладка; `DBG_PORT_SEL=A`. |
| 000 | Внутренняя Flash, JTAG_B на PD0–PD4 | `DBG_PORT_SEL=B`; аналоговые функции PD0–PD4 заняты. |
| 101 | UART2 Boot ROM на PD0/PD1 | `DBG_PORT_SEL=OFF`; выбрать VCP либо внешний UART 3,3 В. |
| 110 | UART2 Boot ROM на PF0/PF1 | `DBG_PORT_SEL=OFF`; исключить нагрузку D11/D13. |
| 111 | Тестовый режим JTAG_A TAP | Не штатный режим пользовательской программы. |

`DBG_PORT_SEL` — пять трёхконтактных селекторов общей шины TCK, TMS/SWDIO, TDI, TDO/SWO и nTRST. Все пять переводят в A, B или OFF согласованно; смешанные положения относятся только к специальной диагностике. Общие `TARGET_nRESET` и `DBG_VTREF` не выбираются между JTAG_A и JTAG_B. Локальный nTRST удерживается в неактивном состоянии подтяжкой; стандартный ARM 10-pin не содержит отдельного nTRST.

| Источник отладки | DAP_ROUTE / XP8 | DBG_PORT_SEL | Подключение |
|---|---|---|---|
| Встроенный DAP → локальный К1986 | TARGET | A или B по MODE | USB-C DAP; встроенный транспорт SWD/SWO. |
| Внешний DAP → локальный К1986 | OFF | A или B по MODE | ARM Cortex Debug 10-pin; SWD либо полный четырёхпроводный JTAG. |
| Встроенный DAP → внешняя плата | EXTERNAL | OFF рекомендуется | XP7; локальная DBG-шина отключена от DAP. |

При внешнем отладчике все пять джамперов XP8 снимают. Активный внешний отладчик на ARM 10-pin и `DAP_ROUTE=TARGET` одновременно подключать нельзя. XP7 не служит входом внешнего отладчика к локальному К1986. Перед отладкой встроенный DAP должен видеть фактический VTref 3,3 В выбранной target; при отсутствии VTref его выходы должны оставаться высокоимпедансными.

### UART2 Boot ROM и VCP

Arduino D0/D1 постоянно обслуживает UART1 на PB6/PB5. Отдельный VCP использует UART2 на PD0/PD1 и в базовой комплектации физически отключён: R1005/R1006 установлены, R1105/R1106 = DNP. Для работы VCP снять R1005/R1006 и установить R1105/R1106 совместно; JTAG_B и Morpho CN10.34/CN10.36 от этих выводов будут отключены. Направления: `DAP_VCP_TX` → PD0/UART2_RXD, PD1/UART2_TXD → `DAP_VCP_RX`.

Для `MODE=101` выбрать ровно один источник UART2: встроенный VCP с R1105/R1106 или внешний USB-UART 3,3 В через Morpho с R1005/R1006. JTAG_B должен быть OFF; R1109 и R1206 не установлены. Для `MODE=110` UART2-загрузчик использует PF0/PF1: D11 переключают на PA1 либо отключают от внешней нагрузки, D13 освобождают от shield. В обоих режимах после установки MODE выполняют полный power cycle. RS-232 и USB-UART с уровнями 5 В подключать нельзя.

## USB-C К1986

Отдельный USB-C target подключён к DP (вывод 9) и DN (вывод 10) К1986 и постоянно работает как Device/UFP/Sink. На CC1/CC2 установлены отдельные Rd 5,1 кОм, 1 % к GND. Контакты D+ и D− каждой стороны розетки объединены по своему сигналу; у разъёма стоит USBLC6-2SC6, а у VBUS — C6 = 100 нФ. D+/D− подключены к МК через предварительные последовательные R21/R22 = 22 Ом; итоговые номиналы уточняются при проверке сигнала. Экраны разъёма соединены с GND. `USB_VBUS` поступает на свой вход T-селектора напрямую, без дополнительного eFuse платы.

USB-контроллер К1986 поддерживает другие роли на уровне периферии, однако этот разъём электрически реализован только как UFP/Sink; прошивка должна оставлять `HSCR.HOST_MODE=0`. Host/Source, USB PD и напряжения VBUS выше номинальных 5 В не поддерживаются. Для USB требуется тактирование блока 48 МГц. Контроль присутствия VBUS и влияние errata 0033 на состояния DP/DN при запуске и Standby подлежат проверке.

## Сброс, тактирование и локальные элементы

`TARGET_nRESET` имеет подтяжку к `+3V3_TGT` и C1 = 100 нФ к GND у К1986. Кнопка, встроенный и внешний отладчики, shield могут только притягивать nRESET к GND; активный высокий уровень и подтяжка к 5 В запрещены. Сброс К1986 электрически отделён от NRST STM32F103 и не заменяет power cycle после изменения MODE.

Штатный HSE К1986 получает 8 МГц от `DAP_MCO`: PA8 STM32F103 → R109 = 22 Ом → `DAP_MCO_Line` → R1003 = 0 Ом → OSC_IN. При автономной работе без DAP следует использовать внутренний HSI или альтернативный источник. Локальный HSE-кварц через R1103/R1213 и его C2/C3 штатно DNP; готовый внешний генератор может подаваться на CN7.29 через R1203 (DNP) вместо R1003. R1113 к CN7.31 в этих режимах оставляют DNP. Для MCO и внешнего генератора применяется `HSEBYP=1`, для локального кварца — `HSEBYP=0`; источники одновременно не подключают. Локальный LSE-кварц с C4/C5 и R1107/R1108 тоже штатно DNP, тогда PE6/PE7 доступны на Morpho через R1007/R1008.

Пользовательские LED1–LED4 подключены к PA1, PA2, PA3 и PA5 через индивидуальные резисторы и активны высоким уровнем. Цвета и номиналы резисторов выбираются после выбора светодиодов; при использовании соответствующих GPIO как входов нагрузку LED следует учитывать или снять его резистор. Кнопка подключена к PB9 через R9. WAKEUP подтянут к питанию К1986 и может быть выведен на CN7.3 установкой R13 (DNP); STANDBY является выходом К1986 на CN7.4 через последовательный резистор.

См. также [общее описание](01_Общее_описание_платы.md), [питание](02_Питание_и_внешние_выходы.md) и [программатор](04_Программатор_распиновка.md).
