Miluino/Miluino_MA1_hardware/docs/Техническая документация/04_Программатор_распиновка.md

# STM32F103CBU6: распиновка встроенного программатора

## Роль и питание

STM32F103CBU6 (DD2, UFQFPN48) образует аппаратную основу встроенного CMSIS-DAP. Предусмотрены CMSIS-DAP v2 через USB Full Speed, SWD к локальному К1986 или внешней target, приём SWO, управление nRESET и питанием от USB-C DAP, а также опциональный VCP на UART2 К1986. Встроенная прошивка выполняет SWD; полный JTAG локального К1986 доступен внешнему адаптеру через отдельный ARM Cortex Debug 10-pin. Питание DD2 `+3V3_DAP` формируется от собственного USB-C независимо от `+3V3_TGT`; земля общая.

## Все выводы STM32F103CBU6

`NC` означает, что обязательная функция в проектной схеме не назначена. Значения выводов и соединений относятся к аппаратному проекту; функции CMSIS-DAP и VCP требуют соответствующей прошивки.

| № | Вывод DD2 | Назначение и электрическое соединение |
|---:|---|---|
| 1 | VBAT | `+3V3_DAP`, локальная развязка 100 нФ; отдельной батареи нет. |
| 2 | PC13 | NC, резерв. |
| 3 | PC14/OSC32_IN | NC, LSE не установлен. |
| 4 | PC15/OSC32_OUT | NC, LSE не установлен. |
| 5 | PD0/OSC_IN | Вход кварца HSE 8 МГц, нагрузочный конденсатор к GND. |
| 6 | PD1/OSC_OUT | Выход кварца HSE 8 МГц, нагрузочный конденсатор к GND. |
| 7 | NRST | `DAP_MCU_NRST` на XP5.5, C107 = 100 нФ к GND; отдельной кнопки нет. |
| 8 | VSSA | GND. |
| 9 | VDDA | `+3V3_DAP`, локальные 10 нФ и 1 мкФ к VSSA. |
| 10 | PA0 | `nDAP_VTREF_PRESENT`, вход NMOS-детектора выбранной target. |
| 11 | PA1 | `DAP_TARGET_PWR_EN`, активный высокий уровень для внешних выходов DAP и P-MOSFET ветви target. |
| 12 | PA2/USART2_TX | `DAP_VCP_TX_Line`, XP6.1; через DNP R1105 может идти на PD0/RX К1986. |
| 13 | PA3/USART2_RX | `DAP_VCP_RX_Line`, XP6.2; через DNP R1106 может получать PD1/TX К1986. |
| 14 | PA4 | NC. |
| 15 | PA5 | NC; не объединять с PB13/SWCLK. |
| 16 | PA6 | NC. |
| 17 | PA7 | NC. |
| 18 | PB0 | NC. |
| 19 | PB1 | NC. |
| 20 | PB2/BOOT1 | 10 кОм к GND, штатная загрузка из Flash. |
| 21 | PB10 | NC. |
| 22 | PB11/USART3_RX | `DAP_SWO_RX` от XP8.10 через последовательные 100 Ом. |
| 23 | VSS_1 | GND. |
| 24 | VDD_1 | `+3V3_DAP`, локальные 100 нФ к GND. |
| 25 | PB12 | Управление внешним NMOS 2N7002 линии `DAP_nRESET`; GPIO высокий → nRESET низкий. |
| 26 | PB13 | `DAP_SWCLK` через последовательный резистор к XP8.7. |
| 27 | PB14 | Двунаправленный `DAP_SWDIO` через последовательный резистор к XP8.8. |
| 28 | PB15 | `DAP_USB_PULLUP_EN_n`, управление P-MOSFET внешней USB D+ подтяжки. |
| 29 | PA8/MCO | `DAP_MCO` → R109 = 22 Ом → `DAP_MCO_Line`, штатные 8 МГц для OSC_IN К1986 через R1003. |
| 30 | PA9/USART1_TX | `DAP_LOG_TX`, сервисный неблокирующий логгер. |
| 31 | PA10/USART1_RX | `DAP_LOG_RX`, сервисный неблокирующий логгер. |
| 32 | PA11/USB_DM | USB-C DAP D− через R119 = 22 Ом и USBLC6-2SC6. |
| 33 | PA12/USB_DP | USB-C DAP D+ через R118 = 22 Ом и USBLC6-2SC6; внешняя 1,5 кОм подтяжка на стороне MCU. |
| 34 | PA13/SWDIO | `DAP_MCU_SWDIO` на XP5.2 для прошивки самого DD2. |
| 35 | VSS_2 | GND. |
| 36 | VDD_2 | `+3V3_DAP`, локальные 100 нФ к GND. |
| 37 | PA14/SWCLK | `DAP_MCU_SWCLK` на XP5.4 для прошивки самого DD2. |
| 38 | PA15 | NC. |
| 39 | PB3 | Не назначен обязательной функции; использование требует уточнения схемы и прошивки. |
| 40 | PB4 | NC. |
| 41 | PB5 | NC, возможный резерв для индикации после выбора схемы. |
| 42 | PB6 | NC, возможный резерв для индикации после выбора схемы. |
| 43 | PB7 | NC. |
| 44 | BOOT0 | 10 кОм к GND, штатная загрузка из Flash. |
| 45 | PB8 | NC. |
| 46 | PB9 | NC. |
| 47 | VSS_3 | GND. |
| 48 | VDD_3 | `+3V3_DAP`, локальные 100 нФ и общая ёмкость 4,7 мкФ к GND. |

Открытая площадка UFQFPN48 соединяется с GND. VBAT и VDDA получают питание того же домена `+3V3_DAP`; между доменами DD2 и К1986 нет преобразователей логических уровней. Кварц DD2 — 8 МГц; номиналы C108/C109 (предварительно 18 пФ) рассчитываются по нагрузочной ёмкости выбранного кварца. C100–C102 — локальные 100 нФ VDD, C103 — 4,7 мкФ, C104/C105 — 10 нФ/1 мкФ VDDA, C106 — 100 нФ VBAT, C107 — 100 нФ NRST.

## USB-C программатора

USB-C DAP имеет фиксированную роль Device/UFP/Sink. На CC1 и CC2 стоят отдельные Rd R111/R110 = 5,1 кОм, 1 % к GND. Контакты A6/B6 розетки объединены в D+, A7/B7 — в D−. PA12 и PA11 подключены к ним через предварительные последовательные R118/R119 = 22 Ом; у разъёма установлена низкоёмкостная сборка USBLC6-2SC6 для D+/D−, а на VBUS — C110 = 100 нФ. VBUS сборки соединён с `USB_DAP_VBUS`, её земля — с общей GND коротким проводником. Экран разъёма соединён с GND. USB Power Delivery и повышенные напряжения VBUS не поддерживаются.

Внешняя подтяжка D+ R115 = 1,5 кОм к `+3V3_DAP` включается P-MOSFET под управлением PB15. R117 = 1 кОм стоит в цепи затвора, R116 = 10 кОм подтягивает его к истоку: высокий уровень или high-Z PB15 оставляет подтяжку выключенной, низкий включает её. Прошивка включает подтяжку только после готовности тактирования USB 48 МГц и инициализации интерфейса. USBLC6-2SC6 защищает сигнальную пару от ESD, но не заменяет ограничитель тока VBUS и не отменяет CC- и последовательные резисторы.

От `USB_DAP_VBUS` питается внутренний LDO `+3V3_DAP`, первый TPS2553-1 внешних выходов DAP и отдельный P-MOSFET путь `+5V_DAP_USB` к T-селектору питания К1986. Эти два управляемых силовых пути включаются PA1 через `DAP_TARGET_PWR_EN`; при сбросе они выключены. Ток локальной target не проходит через TPS2553-1 внешних выходов. Токовый бюджет и запрет обратной подачи приведены в [документе по питанию](02_Питание_и_внешние_выходы.md).

## Сервисный SWD и UART

| Контакт XP5 | Сигнал | Назначение |
|---:|---|---|
| 1 | `+3V3_DAP` | Только VTref внешнего SWD-адаптера; не вход питания платы. |
| 2 | `DAP_MCU_SWDIO` | PA13. |
| 3 | GND | Общая земля. |
| 4 | `DAP_MCU_SWCLK` | PA14. |
| 5 | `DAP_MCU_NRST` | NRST DD2. |

XP5 — установленная гребёнка 1×5, 2,54 мм, для первичной прошивки, восстановления и отладки самого DD2. BOOT0 и PB2/BOOT1 удерживаются в нуле отдельными 10 кОм; сервисный XP9 не применяется. XP6.1 выведен от PA2/USART2_TX, XP6.2 — к PA3/USART2_RX; направления указаны относительно DD2. UART2 target соединяется с ними только в альтернативной комплектации R1105/R1106 вместо R1005/R1006. Arduino D0/D1 остаются на UART1 К1986.

## Доступ к target: XP7, XP8 и ARM 10-pin

### XP7 для внешней target

| Контакт XP7 | Сигнал | Направление относительно DAP |
|---:|---|---|
| 1 | `EXT_VTREF` | Вход фактического логического питания внешней target, номинально 3,3 В. |
| 2 | SWCLK | Выход. |
| 3 | GND | Общая земля. |
| 4 | SWDIO | Двунаправленный. |
| 5 | nRESET | Выход open-drain для притягивания к GND. |
| 6 | SWO | Вход трассировки. |

XP7 не подаёт питание через VTref и не поддерживает полный JTAG. Отдельные `+5V_DAP_OUT`/`+3V3_DAP_OUT` могут питать внешнюю target в пределах общего ключа; GND берётся рядом. Внешняя плата при любом источнике питания возвращает своё фактическое 3,3 В на XP7.1.

### XP8 / DAP_ROUTE

Гребёнка XP8 3×5 с шагом 2,54 мм физически переключает SWCLK, SWDIO, nRESET, VTref и SWO. При виде на плату сверху контакты 1–5 образуют EXT, 6–10 — DAP, 11–15 — LOC; контакт 1 находится сверху слева.

| Строка | EXT | DAP | LOC |
|---|---|---|---|
| VTref | 1 `EXT_VTREF` | 6 `DAP_VTREF` | 11 `LOC_VTREF` |
| SWCLK | 2 `EXT_SWCLK` | 7 `DAP_SWCLK` | 12 `LOC_SWCLK` |
| SWDIO | 3 `EXT_SWDIO` | 8 `DAP_SWDIO` | 13 `LOC_SWDIO` |
| nRESET | 4 `EXT_nRESET` | 9 `DAP_nRESET` | 14 `LOC_nRESET` |
| SWO | 5 `EXT_SWO` | 10 `DAP_SWO` | 15 `LOC_SWO` |

В `EXTERNAL` установлены пять пар EXT–DAP (1–6 ... 5–10), в `TARGET` — пять пар DAP–LOC (6–11 ... 10–15), в `OFF` все джамперы сняты. Все строки переводятся совместно; два джампера в одной строке и смешанная конфигурация запрещены. При `OFF` встроенный DAP физически отсоединён от обеих target, включая VTref и nRESET.

### Внешний ARM Cortex Debug 10-pin

Разъём 2×5, шаг 1,27 мм, подключён к общей локальной DBG-шине перед `DBG_PORT_SEL` и предназначен для внешнего SWD/JTAG-адаптера. Его контакты: 1 VTref, 2 TMS/SWDIO, 3 GND, 4 TCK/SWCLK, 5 GND, 6 TDO/SWO, 7 KEY без штыря, 8 TDI, 9 GND, 10 nRESET. nTRST на нём нет; локальный nTRST удерживается подтяжкой. Перед подключением активного внешнего адаптера XP8 переводят в `OFF`, затем выбирают `DBG_PORT_SEL=A` при MODE=001 либо `B` при MODE=000. Одновременное управление общей DBG-шиной встроенным и внешним DAP запрещено.

## SWD, SWO, VTref и nRESET

PB13 формирует SWCLK, PB14 служит единственной двунаправленной линией SWDIO: во время передачи используется push-pull output, при turnaround и приёме — floating input. Внутренняя подтяжка PB14 к `+3V3_DAP` не применяется; внешняя 100 кОм находится на стороне выбранной target. PB11 принимает SWO через USART3_RX. В JTAG-режиме внешнего адаптера та же линия target работает как TDO, поэтому одновременный TDO и SWO на одном проводнике невозможны.

PB12 через 1 кОм управляет затвором 2N7002; его затвор подтянут 10 кОм к GND, исток заземлён, сток подключён к средней строке nRESET XP8. Высокий уровень PB12 открывает транзистор и формирует низкий nRESET. При сбросе DD2 target nRESET отпущен; подтяжка находится на стороне target к её 3,3 В. DD2 и К1986 имеют независимые линии сброса.

Через XP8 выбранный `DAP_VTREF` поступает на NMOS-детектор: последовательно 1 кОм к затвору, 10 кОм затвор–GND, 10 кОм подтяжка стока к `+3V3_DAP` и вход PA0. Низкий `nDAP_VTREF_PRESENT` означает обнаруженное напряжение, высокий — его отсутствие. Это **детектор присутствия**, не точный компаратор диапазона: плата поддерживает target только с логикой 3,3 В, ориентир VTref 3,0...3,6 В. При отсутствующем VTref прошивка должна отпускать nRESET, переводить SWCLK/SWDIO в high-Z и отключать SWO.

## MCO, VCP и индикация

PA8/MCO штатно предоставляет К1986 сигнал HSE 8 МГц через R109 = 22 Ом и установленный R1003 = 0 Ом на стороне OSC_IN. При выборе локального кварца или внешнего генератора R1003 снимается, а формирование MCO в прошивке DAP отключается. Выключенный DAP не является источником MCO; автономная target должна использовать HSI или иной установленный источник.

VCP предусмотрен по PA2/PA3 и UART2 К1986; его соединение через R1105/R1106 штатно DNP. PA9/PA10 выделены под отдельный сервисный логгер DAP, который не должен задерживать USB, SWD или SWO. `DAP_COM_LED` функционально предусмотрен, но GPIO, схема двухцветной индикации, модели светодиодов и их резисторы не выбраны. Выход `FAULT` ключа внешнего питания DAP остаётся только на локальном индикаторе, без связи с DD2 или К1986; модель LED и резистор также не выбраны.

## Требования к прошивке и проверке

Прошивка должна реализовывать CMSIS-DAP v2 через USB bulk, SWD с переключением JTAG→SWD для К1986, управление nRESET с учётом инверсии PB12, приём SWO, безопасное отключение выводов при ошибке и отсутствии VTref, при необходимости CDC ACM/VCP, уникальный USB serial number и неблокирующий логгер. Встроенный полный JTAG не требуется; заявляемая возможность JTAG в CMSIS-DAP должна быть выключена. Выходы питания от DAP разрешаются только после USB `SET_CONFIGURATION` на 500 мА и выключаются при suspend, reset, deconfiguration и потере VBUS. Возможности и объём Flash/SRAM выбранной прошивки проверяются до выпуска платы; 128 Кбайт Flash и 20 Кбайт SRAM DD2 сами по себе не подтверждают, что полный набор функций поместится.

См. также [общее описание](01_Общее_описание_платы.md), [питание](02_Питание_и_внешние_выходы.md) и [К1986](03_К1986_распиновка_и_программирование.md).
