Miluino/Miluino_MA1_hardware/docs/STM32F103_DAP_pinout.md

# Распиновка DD2 встроенного программатора

## 1. Назначение и источники

Документ фиксирует распиновку микроконтроллера DD2 встроенного программатора на исходной плате и назначение его внешних цепей. Он предназначен как исходная карта для переноса программатора с прошивки ST-Link на CMSIS-DAP.

Источники:

- [исходная принципиальная схема ДФТВ.434519.003Э3, лист 2](../datasheets/ДФТВ.434519.003Э3.pdf#page=2);
- [STM32F103x8/xB, раздел 3 «Pinouts and pin description», страницы 21-33](../datasheets/stm32f103cb.pdf#page=21), в особенности рисунки 8 и 9 и таблица 5 для `LQFP48/UFQFPN48`.

На текущей плате установлена микросхема с маркировкой `STM32F103CBU6`:

- `C` - 48 выводов;
- `B` - 128 Кбайт Flash;
- `U` - корпус UFQFPN48;
- `6` - температурный диапазон от -40 до +85 °C;
- объём SRAM для STM32F103CB составляет 20 Кбайт.

Таким образом, приведённая ниже нумерация UFQFPN48 соответствует фактически установленному DD2. Доступные 128 Кбайт Flash и 20 Кбайт SRAM являются исходными ресурсами для прошивки CMSIS-DAP v2, CDC/VCP, SWO и индикации.

В исходной схеме толстые линии `T1`, `T2` и `T3` используются как графические жгуты. Они не означают электрическое объединение всех входящих в них проводников; электрическое назначение определяется подписями отдельных цепей.

## 2. Полная таблица выводов DD2

Столбец «Рекомендуемое подключение новой платы» фиксирует текущую проектную рекомендацию для CMSIS-DAP. Формулировки «кандидат» и «не утверждено» не являются окончательным назначением цепи и требуют отдельного согласования перед выпуском схемы.

| № | Вывод STM32 | Функция из даташита, существенная для программатора | Назначение в программаторе | Рекомендуемое подключение новой платы | Подключение на исходной схеме | Комментарий |
| --: | --- | --- | --- | --- | --- | --- |
| 1 | `VBAT` | Питание резервного домена | Резервный домен питается от общего питания DD2; отдельная батарея отсутствует | `+3V3_DAP` | `+3,3В_In` | Отдельная батарея не требуется |
| 2 | `PC13-TAMPER-RTC` | GPIO, TAMPER/RTC | Не используется | NC | Не подключён | Возможный резерв для низкоскоростной индикации; назначение не утверждено |
| 3 | `PC14-OSC32_IN` | Вход LSE | Кварц 32,768 кГц отсутствует | NC | Не подключён | LSE для CMSIS-DAP не требуется |
| 4 | `PC15-OSC32_OUT`  | Выход LSE | Кварц 32,768 кГц отсутствует | NC | Не подключён | LSE для CMSIS-DAP не требуется |
| 5 | `PD0-OSC_IN` | Вход HSE; после ремапа `PD0` | Вход основного кварцевого генератора DD2 | кварц 8 МГц, `C_LOAD_IN` -> GND | ZQ3, C20 на GND | Нагрузочную ёмкость рассчитать по `CL` выбранного кварца с учётом паразитной ёмкости |
| 6 | `PD1-OSC_OUT` | Выход HSE; после ремапа `PD1` | Выход основного кварцевого генератора DD2 | кварц 8 МГц, `C_LOAD_OUT` -> GND | ZQ3, C24 на GND | Нагрузочную ёмкость рассчитать по `CL` выбранного кварца с учётом паразитной ёмкости |
| 7 | `NRST` | Аппаратный сброс DD2 | Сброс микроконтроллера программатора | `C_NRST=100 нФ` -> GND, `DAP_MCU_NRST` -> XP5.5 | R14 к `+3,3В_In`, C17 к GND | Внешняя подтяжка и отдельная кнопка не требуются; сброс доступен внешнему SWD-адаптеру |
| 8 | `VSSA` | Аналоговая земля | Аналоговая земля DD2 | GND | GND | Подключить непосредственно к земле рядом с DD2 |
| 9 | `VDDA` | Аналоговое питание | Аналоговое питание DD2, включая АЦП | `+3V3_DAP` -> 0 Ом/FB; 10 нФ + 1 мкФ -> `VSSA` | `+3,3В_In` | Предусмотреть выбор 0 Ом или феррита и разместить развязку рядом с выводом |
|  10 | `PA0-WKUP` | `ADC12_IN0`, `USART2_CTS`, `TIM2_CH1_ETR` | Дискретный контроль наличия питания выбранной target | `nDAP_VTREF_PRESENT` от NMOS-детектора | Цепь `T1`, связанная с `VDD_TRG` через VD1, R11, R12 и R13 | Gate: 1 кОм последовательно и 10 кОм к source; drain: 10 кОм к `+3V3_DAP`; детектор не измеряет точное напряжение |
|  11 | `PA1` | `ADC12_IN1`, `USART2_RTS`, `TIM2_CH2` | Управление питанием внешних выходов DAP и ветвью питания К1986 от USB-C DAP | `DAP_TARGET_PWR_EN` | Не подключён | Активный высокий уровень; путь к GND через 1 кОм до gate NMOS и 10 кОм от gate удерживает оба тракта выключенными при сбросе и high-Z |
|  12 | `PA2` | `USART2_TX`, `ADC12_IN2`, `TIM2_CH3` | Передача UART от DD2 к target; физический канал будущего VCP | `DAP_VCP_TX_Line` -> XP6.1 | `D5` -> XP6.1 `TxData` | Выход DD2 подключается к RX target; XP6 используется как контрольная точка |
|  13 | `PA3` | `USART2_RX`, `ADC12_IN3`, `TIM2_CH4` | Приём UART от target; физический канал будущего VCP | `DAP_VCP_RX_Line` -> XP6.2 | `D3` -> XP6.2 `RxData` | Вход DD2 подключается к TX target; XP6 используется как контрольная точка |
|  14 | `PA4` | `SPI1_NSS`, `USART2_CK`, `ADC12_IN4` | Не используется | NC | Не подключён | Резервный GPIO |
|  15 | `PA5` | `SPI1_SCK`, `ADC12_IN5` | Не используется | NC | `SWCM` -> R21 -> `SWC` | В новой схеме не соединять с PB13 или `DAP_SWCLK` |
|  16 | `PA6` | `SPI1_MISO`, `ADC12_IN6`, `TIM3_CH1` | Не используется | NC | Не подключён | Резервный GPIO |
|  17 | `PA7` | `SPI1_MOSI`, `ADC12_IN7`, `TIM3_CH2` | Не используется | NC | Не подключён | Резервный GPIO |
|  18 | `PB0` | `ADC12_IN8`, `TIM3_CH3` | Не используется | NC | `RSTM` -> R24 -> `RST` | Освобождён после переноса управления nRESET на PB12 |
|  19 | `PB1` | `ADC12_IN9`, `TIM3_CH4` | Не используется | NC | Не подключён | Возможный резерв для индикации |
|  20 | `PB2/BOOT1` | GPIO и вход выбора загрузочного режима `BOOT1` | Фиксация `BOOT1=0` для штатной загрузки из Flash | 10 кОм -> GND | Непосредственно GND | Резистивная подтяжка вместо прямого замыкания сохраняет безопасное использование GPIO после загрузки |
|  21 | `PB10` | `I2C2_SCL`, `USART3_TX`, `TIM2_CH3` | Не используется | NC | Не подключён | Резерв `USART3_TX`, если он потребуется прошивке |
|  22 | `PB11` | `I2C2_SDA`, `USART3_RX`, `TIM2_CH4` | Аппаратный приём SWO через USART3_RX | XP8.10 -> 100 Ом -> `DAP_SWO` | Не подключён | Начальный номинал 100 Ом; окончательно подтвердить устойчивость захвата на прототипе |
|  23 | `VSS_1` | Цифровая земля | Земля DD2 | GND | GND | Подключить непосредственно к земле |
|  24 | `VDD_1` | Цифровое питание | Питание DD2 | `+3V3_DAP`; 100 нФ -> GND | `+3,3В_In` | Разместить конденсатор максимально близко к паре `VDD_1/VSS_1` |
|  25 | `PB12` | `SPI2_NSS`, `I2C2_SMBAI`, `USART3_CK`, `TIM1_BKIN` | Управление nRESET target | PB12 -> 1 кОм -> gate 2N7002; drain -> `DAP_nRESET` -> XP8.9 | `T3` -> R18 -> `SWDM` | Source -> GND, gate -> 10 кОм -> GND; высокий уровень PB12 активирует сброс |
|  26 | `PB13` | `SPI2_SCK`, `USART3_CTS`, `TIM1_CH1N` | Единственный выход формирования SWCLK target | `DAP_SWCLK` -> 22–47 Ом -> XP8.7 | `SWCM` -> R21 -> `SWC` | Единственный push-pull выход SWCLK; последовательный резистор опциональный |
|  27 | `PB14` | `SPI2_MISO`, `USART3_RTS`, `TIM1_CH2N` | Двунаправленная линия SWDIO target | `DAP_SWDIO` -> 22–47 Ом -> XP8.8 | `SWDM` -> R22 -> `SWD` | Push-pull при передаче, floating input при приёме; внутреннюю подтяжку STM32 не включать |
|  28 | `PB15` | `SPI2_MOSI`, `TIM1_CH3N` | Управление внешней подтяжкой USB D+ | `DAP_USB_PULLUP_EN_n` -> 1 кОм -> gate P-MOSFET | Не подключён | Активный низкий уровень; gate подтянут к source (`+3V3_DAP`) резистором 10 кОм |
|  29 | `PA8` | `MCO`, `USART1_CK`, `TIM1_CH1` | MCO на исходной плате не используется | `DAP_MCO` -> 22 Ом -> `DAP_MCO_Line` | Не подключён | Резистор размещается возле PA8; отдельный `R_EN_DAP` не устанавливается |
|  30 | `PA9` | `USART1_TX`, `TIM1_CH2` | Передача отладочных сообщений прошивки DAP | `DAP_LOG_TX` | `Tx`, `LED_ST`; XP5.1 `TxDataPRG`, R19/R20 и HL5 | Логгер не должен блокировать обработку USB, SWD и SWO |
|  31 | `PA10` | `USART1_RX`, `TIM1_CH3` | Приём данных логгера DAP | `DAP_LOG_RX` | `Rx`, `SWOM`; XP5.2 `RxDataPRG`, через R25 к `SWO` | SWO target переносится на PB11/USART3_RX; PA10 используется только как USART1_RX логгера |
|  32 | `PA11` | `USBDM`, `USART1_CTS`, `CANRX`, `TIM1_CH4` | USB Full Speed D- | `DAP_USB_D-` -> R_SER/ESD -> USB-C D- | `DM` -> XS5.2 `D-` | Контакты D- разъёма USB-C объединить; использовать малоёмкостную ESD-защиту и место под согласующий резистор  |
|  33 | `PA12` | `USBDP`, `USART1_RTS`, `CANTX`, `TIM1_ETR` | USB Full Speed D+ | `DP_DAP_USB` -> R_SER/ESD -> USB-C D+ | `DP` -> XS5.3 `D+` | Подтяжку 1,5 кОм подключить к стороне PA12 до R_SER; контакты D+ USB-C объединить |
|  34 | `PA13` | `JTMS/SWDIO` после сброса | Штатный SWDIO для программирования и отладки самого DD2 | `DAP_MCU_SWDIO` -> XP5.2 | Не подключён | Не использовать для других функций |
|  35 | `VSS_2` | Цифровая земля | Земля DD2 | GND | GND | Подключить непосредственно к земле |
|  36 | `VDD_2` | Цифровое питание | Питание DD2 | `+3V3_DAP`; 100 нФ -> GND | `+3,3В_In` | Разместить конденсатор максимально близко к паре `VDD_2/VSS_2` |
|  37 | `PA14` | `JTCK/SWCLK` после сброса | Штатный SWCLK для программирования и отладки самого DD2 | `DAP_MCU_SWCLK` -> XP5.4 | Не подключён | Не использовать для других функций |
|  38 | `PA15` | `JTDI`; после отключения JTAG может использоваться как GPIO | Не используется | NC | R17 и VT1, связанные с цепью подтяжки USB D+ | Управление USB-подтяжкой перенесено на PB15; PA15 не требует отключения JTAG ради этой функции |
|  39 | `PB3` | `JTDO`; после ремапа `TRACESWO`, `SPI1_SCK`, `TIM2_CH2` | Назначение по листу 2 однозначно не определяется; до появления дополнительного источника считать неиспользуемым и не назначать обязательную функцию CMSIS-DAP | NC | Линия входит в графический жгут без подписанной конечной цепи | Использовать только после отключения JTAG и отдельного утверждения назначения |
|  40 | `PB4` | `JNTRST`; после ремапа GPIO, `SPI1_MISO`, `TIM3_CH1` | Не используется | NC | Не подключён | Использовать только после отключения JTAG и отдельного утверждения назначения |
|  41 | `PB5` | GPIO, `I2C1_SMBAI`; после ремапа `SPI1_MOSI`, `TIM3_CH2` | Не используется | NC | Не подключён | Возможный резерв для индикации |
|  42 | `PB6` | `I2C1_SCL`, `TIM4_CH1`; после ремапа `USART1_TX` | Не используется | NC | Не подключён | Возможный резерв для индикации |
|  43 | `PB7` | `I2C1_SDA`, `TIM4_CH2`; после ремапа `USART1_RX` | Не используется | NC | Не подключён | Резервный GPIO |
|  44 | `BOOT0` | Выбор области загрузки | Постоянная штатная загрузка из Flash | 10 кОм -> GND | R15 к GND; XP9.2 позволяет соединить с XP9.1 `+3,3В_In` | XP9 удаляется; первичная прошивка и восстановление выполняются через SWD |
|  45 | `PB8` | `TIM4_CH3`; после ремапа `I2C1_SCL`, `CANRX` | Не используется | NC | Не подключён | Резервный GPIO |
|  46 | `PB9` | `TIM4_CH4`; после ремапа `I2C1_SDA`, `CANTX` | Не используется | NC | Не подключён | Резервный GPIO |
|  47 | `VSS_3` | Цифровая земля | Земля DD2 | GND | GND | Подключить непосредственно к земле |
|  48 | `VDD_3` | Цифровое питание | Питание DD2 | `+3V3_DAP`; 100 нФ -> GND | `+3,3В_In` | Разместить конденсатор рядом с `VDD_3/VSS_3`; добавить общий bulk-конденсатор питания DD2 |

## 3. Сводная карта интерфейсов программатора

| Функция | Выводы DD2 | Цепь исходной схемы | Примечание для CMSIS-DAP |
|---|---|---|---|
| USB D- | PA11, вывод 32 | `DM` | Сохранить |
| USB D+ | PA12, вывод 33 | `DP` | Сохранить |
| Управление USB-подтяжкой | PB15, вывод 28 | R17, VT1, R23, R26 | `DAP_USB_PULLUP_EN_n`; внешний P-MOSFET, активный низкий уровень |
| SWCLK target | PB13, вывод 26 | `SWCM` -> R21 -> `SWC` | Единственный push-pull выход; PA5 в новой схеме не подключается к SWCLK |
| SWDIO target | PB14, вывод 27 | `SWDM` -> R22 -> `SWD` | Один двунаправленный GPIO, переключаемый между push-pull output и floating input |
| nRESET target | PB12, вывод 25 | `RSTM` -> R24 -> `RST` | Внешний 2N7002 формирует open-drain; подтяжка находится на target-стороне |
| SWO target | PB11, вывод 22 | На исходной схеме отсутствует | `USART3_RX`, последовательно 100 Ом |
| VTref target | PA0, вывод 10 | `VDD_TRG` -> VD1/R11/R12/R13 -> `T1` | NMOS-детектор присутствия с активным низким выходом; XP7 не должен питать внешнюю плату |
| VCP TX | PA2, вывод 12 | `D5` -> XP6.1 | TX относительно DD2, подключается к RX target |
| VCP RX | PA3, вывод 13 | `D3` -> XP6.2 | RX относительно DD2, подключается к TX target |
| Логгер DAP | PA9/USART1_TX; PA10/USART1_RX | `Tx`/`Rx` исходного сервисного UART | `DAP_LOG_TX` и `DAP_LOG_RX`; реализация должна быть неблокирующей |
| Управление питанием от DAP | PA1, вывод 11 | На исходной схеме отсутствует | `DAP_TARGET_PWR_EN`, активный высокий уровень; напрямую управляет `EN` TPS2553-1 и через NMOS — P-MOSFET ветви К1986 |
| Индикатор COM | GPIO не выбран | На исходной схеме отсутствует | `DAP_COM_LED` сохраняется; вывод и схема подключения будут утверждены отдельно, см. [CMSIS_DAP_indication.md](CMSIS_DAP_indication.md) |
| MCO target | PA8, вывод 29 | На исходной схеме отсутствует | Согласован для новой схемы через последовательный резистор 22 Ом; отключение со стороны target выполняет R1003 |

## 4. Разъёмы, связанные с DD2

### 4.1. XP5 - сервисный SWD самого DD2

XP5 выполняется как установленная однорядная гребёнка 1x5 с шагом 2,54 мм:

| Контакт | Сигнал | DD2 / назначение |
|---:|---|---|
| 1 | `+3V3_DAP` | VTref внешнего SWD-адаптера; не является входом питания платы |
| 2 | `DAP_MCU_SWDIO` | PA13/SWDIO, вывод 34 |
| 3 | GND | Общая земля |
| 4 | `DAP_MCU_SWCLK` | PA14/SWCLK, вывод 37 |
| 5 | `DAP_MCU_NRST` | NRST, вывод 7 |

Контакт 1 выполняется квадратной площадкой и отмечается на шелкографии. PA13 и PA14 не используются другими функциями, SWO самого DD2 на XP5 не выводится. XP5 предназначен для первичной прошивки, восстановления и полной отладки STM32F103 внешним SWD-адаптером.

### 4.2. XP6 - UART target

| Контакт | Цепь | DD2 |
|---:|---|---|
| 1 | `TxData` | PA2/USART2_TX, вывод 12 |
| 2 | `RxData` | PA3/USART2_RX, вывод 13 |

Направления указаны относительно DD2.

### 4.3. XP7 - внешний target

| Контакт | Цепь | Назначение |
|---:|---|---|
| 1 | `EXT_VTREF` | Вход опорного напряжения target |
| 2 | `SWCLK` | Тактирование SWD |
| 3 | `Общий` | GND |
| 4 | `SWDIO` | Двунаправленные данные SWD |
| 5 | `NRST` | Сброс target |
| 6 | `SWO` | Последовательная трассировка target |

XP7 не предназначен для питания внешней target. В новой ревизии поддерживаются только target с логическими уровнями 3,3 В; номинальное значение `EXT_VTREF` равно 3,3 В, рабочий ориентир для контроля наличия питания — 3,0...3,6 В.

Для намеренного питания внешней target от программатора предусматриваются отдельные контакты `+5V_DAP_OUT` и `+3V3_DAP_OUT`. Они не являются частью XP7 и не соединяются с `EXT_VTREF` на стороне программатора; GND берётся с расположенного рядом `SPARE JMP`. При использовании `+5V_DAP_OUT` внешняя плата самостоятельно формирует логическое питание 3,3 В; во всех случаях она должна вернуть своё фактическое VDD на `EXT_VTREF`.

### 4.4. XP8 - исходная коммутация локальной target

| Контакт | Цепь программатора | Цепь локальной target |
|---:|---|---|
| 1 | `SWCLK` / `SWC` | - |
| 2 | - | `SWCLK_TARG` / `SWCT` |
| 3 | `SWDIO` / `SWD` | - |
| 4 | - | `SWDIO_TARG` / `SWDT` |

Исходный XP8 коммутирует только SWCLK и SWDIO. Принятая архитектура новой ревизии предусматривает отдельный пятиканальный `DAP_ROUTE=EXTERNAL/OFF/TARGET`, но эта переработка не является частью зафиксированной здесь исходной распиновки DD2.

### 4.5. XP8 - DAP_ROUTE новой ревизии

В новой ревизии XP8 выполняется в виде гребёнки 3x5 с шагом 2,54 мм. Нумерация задана по столбцам при виде на плату сверху: контакты 1-5 образуют столбец EXT, 6-10 - столбец DAP, 11-15 - столбец LOC. Контакт 1 находится сверху слева, строка VTref является верхней. На шелкографии столбцы обозначаются `EXT | DAP | LOC`; состояние `DAP_ROUTE=TARGET` соответствует подключению встроенного DAP к столбцу `LOC`.

| Строка | EXT | DAP | LOC |
| --- | ---: | ---: | ---: |
| VTref  |  1: `EXT_VTREF` |  6: `DAP_VTREF` |  11: `LOC_VTREF` |
| SWCLK  |  2: `EXT_SWCLK` |  7: `DAP_SWCLK` |  12: `LOC_SWCLK` |
| SWDIO  |  3: `EXT_SWDIO` |  8: `DAP_SWDIO` |  13: `LOC_SWDIO` |
| nRESET | 4: `EXT_nRESET` | 9: `DAP_nRESET` | 14: `LOC_nRESET` |
| SWO | 5: `EXT_SWO` | 10: `DAP_SWO` | 15: `LOC_SWO` |

`DAP_VTREF` получает опорное напряжение выбранной target и не используется для её питания. После XP8 он через последовательный резистор 1 кОм подключается к gate NMOS; gate подтянут к source резистором 10 кОм, source соединён с GND, drain подключён к PA0 и подтянут к `+3V3_DAP` резистором 10 кОм. При наличии VTref транзистор открыт и `nDAP_VTREF_PRESENT=0`, при отсутствии VTref транзистор закрыт и `nDAP_VTREF_PRESENT=1`. При VTref 3,3 В напряжение gate составляет около 3,0 В, поэтому конкретный NMOS должен иметь гарантированную работоспособность при таком уровне.

Этот узел является детектором присутствия, а не измерителем или защитой по уровню напряжения. Он не различает допустимые 3,3 В и ошибочно подключённую target с логикой 1,8 В либо 2,5 В; ограничение «только target 3,3 В» обеспечивается назначением платы и эксплуатационными требованиями. Компаратор вместо согласованного NMOS-детектора не устанавливается.

Режимы установки джамперов:

- `DAP_ROUTE=EXTERNAL`: замкнуты пары 1-6, 2-7, 3-8, 4-9 и 5-10;
- `DAP_ROUTE=TARGET`: замкнуты пары 6-11, 7-12, 8-13, 9-14 и 10-15;
- `DAP_ROUTE=OFF`: все пять джамперов сняты.

Все пять строк должны находиться в одном режиме. Смешанные положения и установка двух джамперов в одной строке запрещены.

## 5. Питание, тактирование и развязка

- `VDD_1`, `VDD_2` и `VDD_3` соединяются с `+3V3_DAP`; возле каждого вывода устанавливается отдельный керамический конденсатор 100 нФ, дополнительно возле `VDD_3` устанавливается общий конденсатор 4,7 мкФ.
- `VDDA` соединяется непосредственно с `+3V3_DAP`; возле VDDA/VSSA устанавливаются 10 нФ и 1 мкФ. Отдельный резистор 0 Ом или ферритовая бусина не устанавливаются.
- `VBAT` соединяется с `+3V3_DAP` и развязывается конденсатором 100 нФ.
- `VSSA`, `VSS_1`, `VSS_2`, `VSS_3` и открытая тепловая площадка UFQFPN48 соединяются с общей GND.
- Основной генератор DD2 выполняется на кварце 8 МГц между PD0/OSC_IN и PD1/OSC_OUT. Нагрузочные конденсаторы рассчитываются по `Cload,in ≈ Cload,out ≈ 2 × (CL − Cstray)` для выбранного кварца.
- NRST DD2 соединяется с GND через 100 нФ и выводится на XP5.5 как `DAP_MCU_NRST`; внешняя подтяжка к `+3V3_DAP` и отдельная кнопка RESET DAP не требуются.
- BOOT0 и PB2/BOOT1 постоянно удерживаются в нуле отдельными резисторами 10 кОм; XP9 не устанавливается.
- PA11/USBDM и PA12/USBDP подключаются к USB-C через последовательные резисторы 22 Ом. Внешняя подтяжка `DP_DAP_USB` сопротивлением 1,5 кОм коммутируется P-MOSFET: source соединён с `+3V3_DAP`, drain — с резистором 1,5 кОм, gate через 1 кОм подключён к PB15 и через 10 кОм — к source.
- Сеть `DAP_USB_PULLUP_EN_n` активна низким уровнем. До инициализации PB15 находится в высокоимпедансном состоянии, резистор gate-source удерживает P-MOSFET закрытым и USB-подтяжку отключённой. Прошивка сначала записывает единицу в выходной регистр PB15, затем переводит вывод в push-pull output и устанавливает ноль только после готовности USB и тактирования 48 МГц.
- USART1_TX на PA9 и USART1_RX на PA10 используются как `DAP_LOG_TX` и `DAP_LOG_RX`. Работа логгера не должна блокировать обработку USB, SWD или SWO; при переполнении программного буфера допускается отбрасывание сообщений.
- `USB_DAP_VBUS` номиналом 5 В питает три тракта: внутренний `TLV76133DCYR`, формирующий `+3V3_DAP`, `TPS2553-1` внешних выходов и отдельный P-MOSFET-тракт питания К1986 через DAP-вход T-селектора. После `TPS2553-1` формируется `+5V_DAP_OUT`, а второй `TLV76133DCYR` с двумя диодами Шоттки формирует защищённый от продолжительного обратного питания `+3V3_DAP_OUT`; для ограничения около 300 мА используется `RILIM=100 кОм, 1 %`.
- `DAP_TARGET_PWR_EN` формируется PA1 и активен высоким уровнем. Сеть напрямую подключается к `EN` TPS2553-1 внешних выходов DAP и через 1 кОм — к gate NMOS 2N7002; gate подтянут к GND резистором 10 кОм, поэтому PA1 получает путь к GND через 11 кОм. Отдельной прямой подтяжки 10 кОм на сети PA1/EN нет. Source 2N7002 соединяется с GND, drain — с gate силового P-MOSFET; gate P-MOSFET подтягивается к его source на `USB_DAP_VBUS` резистором 10 кОм. Drain P-MOSFET формирует `+5V_DAP_USB` для DAP-входа T-селектора. Ток К1986 не проходит через TPS2553-1 внешних выходов.
- После сброса PA1 остаётся high-Z и оба управляемых тракта выключены. Прошивка включает их только после `SET_CONFIGURATION` для USB-конфигурации с заявленным током 500 мА и выключает при suspend, сбросе или деконфигурации USB и потере VBUS.
- При выборе USB-C DAP как источника питания К1986 в бюджете VBUS зарезервировано по 100 мА для К1986 и STM32F103 с запасом по данным производителей и не более 300 мА суммарно на внешние нагрузки выходов DAP и защищённой ветви Output Power (Arduino/Morpho). Расчётный максимум составляет 500 мА. Два TPS2553-1 имеют независимые пределы и аппаратно не ограничивают эту сумму до 300 мА; одновременная постоянная значительная нагрузка обоих каналов не является штатным сценарием. При выборе другого источника питания К1986 бюджеты рассматриваются отдельно.
- На D+/D- каждого USB-C устанавливается `USBLC6-2SC6` по проходной схеме производителя. Сборка не заменяет последовательные резисторы 22 Ом, CC-резисторы и силовую защиту; дополнительных компонентов непосредственно для её работы не требуется.

### 5.1. Конденсаторы STM32F103CBU6

| Нумерация | Номинал | Description в Altium | Описание |
| --- | --- | --- | --- |
| `C100` | `100 нФ, X7R` | `DAP MCU VDD1 local decoupling capacitor` | Локальная развязка `VDD_1`, контакт 24, относительно `VSS_1`, контакт 23. |
| `C101` | `100 нФ, X7R` | `DAP MCU VDD2 local decoupling capacitor` | Локальная развязка `VDD_2`, контакт 36, относительно `VSS_2`, контакт 35. |
| `C102` | `100 нФ, X7R` | `DAP MCU VDD3 local decoupling capacitor` | Локальная развязка `VDD_3`, контакт 48, относительно `VSS_3`, контакт 47. |
| `C103` | `4,7 мкФ, X7R, ≥6,3 В` | `DAP MCU VDD3 bulk decoupling capacitor, 4.7uF, X7R` | Общая накопительная ёмкость питания STM32. По требованию ST подключается около `VDD_3`, контакт 48. |
| `C104` | `10 нФ, X7R или C0G` | `DAP MCU VDDA high-frequency analog decoupling capacitor` | Высокочастотная развязка `VDDA`, контакт 9, относительно `VSSA`, контакт 8. |
| `C105` | `1 мкФ, X7R` | `DAP MCU VDDA bulk analog decoupling capacitor` | Основная развязка аналогового питания `VDDA`. Размещается рядом с `C104`. |
| `C106` | `100 нФ, X7R` | `DAP MCU VBAT local decoupling capacitor` | Развязка `VBAT`, контакт 1. `VBAT` подключается к `+3V3_DAP`, отдельная батарея не используется. |
| `C107` | `100 нФ, X7R` | `DAP MCU NRST reset timing and noise-filter capacitor` | Конденсатор между `NRST`, контакт 7, и GND. Обеспечивает штатную цепь сброса STM32. |
| `C108` | `18 пФ, C0G/NP0, предварительно` | `DAP MCU HSE OSC_IN crystal load capacitor, value TBD` | Нагрузочный конденсатор кварца 8 МГц со стороны `PD0/OSC_IN`. Номинал уточнить по `CL` кварца. |
| `C109` | `18 пФ, C0G/NP0, предварительно` | `DAP MCU HSE OSC_OUT crystal load capacitor, value TBD` | Нагрузочный конденсатор кварца 8 МГц со стороны `PD1/OSC_OUT`. Должен совпадать с `C108` после расчёта. |

`C100-C109` устанавливаются штатно. Номиналы `C108` и `C109` уточняются после выбора кварца по формуле `Cload,in ≈ Cload,out ≈ 2 × (CL − Cstray)`. Дополнительные конденсаторы на линиях USB `D+` и `D-` не устанавливаются. Для выбранного `TLV76133DCYR` шины `+3V3_DAP` отдельно устанавливаются неполярные керамические конденсаторы: входной 1 мкФ X7R не менее 10 В и выходной 4,7 мкФ X7R не менее 6,3 В. Их designator назначается на схеме питания, поэтому в таблицу обвязки STM32 они не включены.

## 6. Ограничения и вопросы для новой схемы

1. Маркировка DD2 подтверждена как `STM32F103CBU6`: 128 Кбайт Flash и 20 Кбайт SRAM. Достаточность этих ресурсов для полного набора CMSIS-DAP v2, CDC/VCP, SWO и индикации необходимо подтвердить сборкой и измерением фактического расхода памяти прошивки.
2. XP5 является единственным штатным интерфейсом первичной прошивки, восстановления и отладки DD2. Контакт `+3V3_DAP` используется внешним SWD-адаптером только как VTref; подавать через него питание на плату запрещено.
3. PB12 управляет внешним NMOS линии nRESET. SWDIO реализуется одним PB14: push-pull output при передаче и floating input при turnaround и приёме. Подтяжка 100 кОм находится на target-стороне; внутреннюю подтяжку PB14 к `+3V3_DAP` включать нельзя.
4. NMOS-детектор `nDAP_VTREF_PRESENT` подтверждает только наличие напряжения и не гарантирует диапазон 3,0...3,6 В. Подключение target с логикой 1,8 В или 2,5 В запрещено; конкретный NMOS необходимо выбрать по гарантированным характеристикам при gate около 3,0 В.
5. Точное назначение PB3 по листу 2 не установлено. Его нельзя считать свободным либо обязательным сигналом до проверки исходного проекта Altium или реальной платы.
6. Для `+3V3_DAP` выбран `TLV76133DCYR`; экраны обоих USB-C напрямую соединены с GND, а `USB_VBUS` USB-C target поступает на T-селектор без дополнительного eFuse или ограничителя тока на плате. Для D+/D- обоих USB-C выбрана сборка `USBLC6-2SC6`; VBUS считается номинальной линией 5 В без USB PD. Ток через USB-C target должен соответствовать разрешённому его хостом значению.
7. Для общих внешних выходов `+5V_DAP_OUT` и `+3V3_DAP_OUT` принята защита `TPS2553-1` с `RILIM=100 кОм, 1 %` и целевым суммарным пределом около 300 мА. Управление `EN` от PA1 через `DAP_TARGET_PWR_EN` утверждено; `+3V3_DAP_OUT` формируется вторым `TLV76133DCYR` с последовательным входным диодом Шоттки и защитным диодом Шоттки от выхода к входу. Для TPS2553-1 приняты неполярные керамические конденсаторы 1 мкФ на входе и 22 мкФ на выходе; эффективная выходная ёмкость при 5 В должна быть не менее 10 мкФ. Остаются выбор конкретных диодов, проверка фактического диапазона ограничения и измерение обратного тока. Одновременная работа с собственным источником внешней target без предусмотренной развязки запрещена.
8. Перед подключением и отключением внешнего SWD-адаптера вся отладочная плата должна быть полностью обесточена. На время программирования DD2 устанавливается `DAP_ROUTE=OFF`; после завершения erase/program/verify плата снова полностью обесточивается.
