Miluino/Miluino_MA1_hardware/docs/CMSIS_DAP_indication.md

# Индикация встроенного CMSIS-DAP

## 1. Назначение и статус документа

Документ фиксирует согласованные функции светодиодной индикации встроенного CMSIS-DAP. Конкретные designator, корпуса, GPIO и размещение на печатной плате указываются только там, где они уже утверждены.

## 2. Индикатор `DAP_COM_LED`

`DAP_COM_LED` предназначен для программной индикации обмена встроенного CMSIS-DAP с компьютером и target. Планируется функциональный аналог двухцветного красно-зелёного индикатора COM на платах STM32 Nucleo.

Индикатор сохраняется в проекте, но его GPIO, электрическая схема и физическое расположение пока не утверждены. PA1 для него не используется: этот вывод назначен активному высоким уровнем сигналу `DAP_TARGET_PWR_EN`. Окончательные состояния красного, зелёного и комбинированного свечения должны быть согласованы вместе с логикой прошивки.

## 3. Аварийный индикатор внешнего питания DAP

Красный светодиод показывает срабатывание выхода `FAULT` микросхемы `TPS2553-1`, защищающей внешние выходы `+5V_DAP_OUT` и `+3V3_DAP_OUT`. Выход `FAULT` имеет активный низкий уровень, относится только к внешним выходам DAP и не подключён ни к STM32F103, ни к К1986; он не показывает состояние отдельного силового ключа питания К1986. Выход `FAULT` ключа Output Power относится к другой ветви и может считываться К1986 через VT1 и штатно не установленный R25.

Согласованная схема:

```text
USB_DAP_VBUS -- 3,3 кОм --|>|-- DAP_EXT_PWR_FAULT_n
                                  |
                              FAULT TPS2553-1
```

Анод светодиода подключается через резистор 3,3 кОм к `USB_DAP_VBUS`, катод — к активному низким уровнем выходу `FAULT`. В штатном состоянии `FAULT` высокоимпедансен и светодиод выключен. При перегрузке, коротком замыкании или обратном напряжении `FAULT` притягивается к GND и светодиод включается. Питание от необработанного `USB_DAP_VBUS`, а не от защищённого выхода, сохраняет индикацию после защёлкивания и отключения `TPS2553-1`.

Рекомендуемый descriptor для Altium: `DAP external power fault indicator LED, red, active-low`.

На текущем листе питания R121=100 кОм подтягивает `FAULT` ключа DAP к `USB_DAP_VBUS`; для одной светодиодной индикации отдельная подтяжка функционально не обязательна, но предусмотрена схемой. Программное чтение этого сигнала не предусматривается; непосредственно подключать цепь светодиода, питаемую от 5 В, к GPIO микроконтроллера нельзя.

## 4. Сводная таблица

| Индикатор | Цвет | Источник управления | Активный уровень | Статус реализации |
|---|---|---|---|---|
| `DAP_COM_LED` | красный/зелёный | прошивка STM32F103 | будет определён схемой включения | GPIO, схема и размещение не утверждены |
| `DAP_EXT_PWR_FAULT_LED` | красный | `FAULT` TPS2553-1 внешних выходов | низкий | схема подключения утверждена, designator не назначен |
