Miluino/Miluino_MA1_hardware/docs/Первоначальный промт.md

Привет
Я инженер-схемотехник, мне нужна будет твоя помощь с анализом даташитов и составлением таблиц для разводки дорожек на печатной плате, которую я разрабатываю. Об этом далее.

Необходимые даташиты находятся в директории ./datasheets
При завершении анализа тех или иных документов создавай необходимый md файл в директории .codex с описанием структуры документов и полезных страниц, чтобы при последующих анализах больших документов сразу читать краткую выжимку из созданного ранее md файла в директории .codex и не анализировать эти документы с нуля
Если есть вопросы - задай перед выполнением данного промта

Далее будет описание моей задачи:

Я перерабатываю существующий проект отладочной платы для микросхемы К1986ВЕ92FI, он называется MDR32 MILUINO
Прошлый разработчик плохо развёл данную отладочную плату, поэтому мне надо её переработать

Текущая разводка отладочной платы находится в "./datasheets/ДФТВ.434519.003Э3.pdf", проанализируй её и учитывай как то, что надо будет переработать 
Документация на всю отладочную плату находится в файле "D:\Job\18shka\Miluino\datasheets\ДФТВ.434519.003ПС.pdf"
Файл с претензиями к текущей реализации отладочной плате находятся в файле "D:\Job\18shka\Miluino\datasheets\Проблемы схематехники милуино_V1.docx"

Сама документация на используемы контроллер К1986ВЕ92FI находится в datasheets/К1986ВЕ92FI, К1986ВЕ92F1I, К1986ВЕ94GI.pdf (анализировать этот документ полностью не надо, проанализируй только распиновку камня. Она находится на страницах 21-31 в таблицах 2 и 3)

Основное требование к разрабатываемой отладочной - максимальная совместимость с модулями расширения для arduino uno и stm nucleo 64 (а именно NUCLEO-F030R8) 
Документация на stm nucleo 64 платы находится в "D:\Job\18shka\Miluino\datasheets\Stm nucleo 64 reference manual.pdf", а для arduino uno r4 в файле "D:\Job\18shka\Miluino\datasheets\Arduino UNO R4 reference manual.pdf"

Для этого на разрабатываемой отладочной плате необходимо повторить функциональную трассировку с arduino uno r4 и stm nucleo 64 (включая возможные переназначения ножек через замыкание через Bridge SBxx)

Если у контроллера К1986ВЕ92FI есть дополнительные выводы, которых нет у stm, то их без проблем можно вынести отдельными пинами
На разрабатываемой плате планируется создание аналогичных мостов, как у stm nucleo SBxx, а также механические переключатели для вывода той или иной ножки контроллера к пину в случае необходимости (например если на один пин у arduino можно завести обычный GPIO и TX, а на камне К1986ВЕ92FI это две разные ножки, то я буду делать механический переключатель между этими двумя ножками К1986ВЕ92FI, чтобы их всё равно можно было одновременно использовать в одном проекте)

После анализа указанных выше документов создай md документ в ./docs с табличным описанием соответствия ножек контроллеров (непосредственные выходы из корпуса контроллера) и пины на отладочных платах stm nucleo (также в зависимости от состояния тех или иных SBxx), arduino uno, а также предложенным тобою соответствием для К1986ВЕ92FI
